keeganmoody33/YADIGGG/physical-design/logo-refinement-brief.md

---
title: "Logo Refinement Brief"
project: yadiggg
status: active-draft
type: brand_identity_brief
tags: [yadiggg, logo, brand-identity, visual-consistency]
backlinks:
  - "[[CONTEXT]]"
  - "[[docs/project-state]]"
  - "[[yadiggg_brand_identity_and_design_guidelines]]"
  - "[[physical-design/render-consistency-protocol]]"
---

# yadiggg Logo Refinement Brief

## Purpose

This brief defines the direction for refining the yadiggg logo so it supports the locked physical product direction instead of drifting into unrelated merch, packaging, or generic record-store iconography.

## Source Materials Reviewed

| Asset | Observed content | Role |
|---|---|---|
| `IMG_3581_converted.png` | Hand-drawn notebook sketch with rough black mark, red shovel/speaker head, green wave/energy strokes, handwritten `yadiggg.xyz` | Primary conceptual source |
| `yadigggsketch_rendered.png` | Cropped/cleaned version of the same sketch; large diagonal handle, red triangular/conical head, sweeping green/black wave marks | Primary conceptual source |
| `Ab0366a7e4d1c4f86ba5eb0a115a0dd80k.png` | Polished orange-on-black graphic with record circle, shovel/needle shape, and `yadiggg` wordmark | Reference-only / partially rejected |
| `yadiggg_brand_identity_and_design_guidelines.md` | Defines the intended metaphor: shovel digging downward, speaker cone in the shovel head, neon soundwave arcs, compact geometric wordmark | Active design requirement |

## Core Logo Metaphor

The refined logo should express:

> A shovel-speaker mark: a shovel digging into vinyl/ground, where the shovel head also reads as a red speaker cone and emits green sound/light-wave energy.

It should work at two distances:

1. **Small / far away**: reads as a shovel digging downward.
2. **Large / close up**: reveals the speaker-cone head and soundwave/energy arcs.

## What Must Be Preserved

- `yadiggg` as the wordmark, not `Crate IQ`.
- Shovel/digging metaphor.
- Audio/speaker metaphor.
- Vinyl/record/crate-digging culture.
- Raw underground energy, but cleaned into a usable hardware brand mark.
- Compatibility with the locked product CMF: smoke-clear shell, dark internals, amber/orange control, monochrome display.

## What Must Change

- The rough sketch must become a scalable vector-like mark.
- The shovel must not read as a generic spade or random microphone stand.
- The polished orange logo should not remain the final direction because it loses the red speaker cone and neon wave energy from the sketch.
- The logo should not be merch-first or oversized on the hardware.
- The wordmark should be cleaner and more controlled than the handwritten `.xyz` sketch.

## Color Direction

| Role | Color | Notes |
|---|---|---|
| Primary dark | Obsidian Charcoal `#1A1A1D` | Main background / hardware-system anchor |
| Hardware accent | Amber Orange `#E07A5F` | Scan-button and warm brand accent |
| Speaker focal point | Speaker Red `#D83232` | Use sparingly inside the shovel/speaker head |
| Energy accent | Neon Wave Green `#72FF66` | Sound/light arcs only; not the whole logo |
| Neutral | Cream White `#F4F1DE` | Alternate contrast color for screen/etch applications |

## Three Refinement Routes

### Route 1: Hardware Badge Mark

A compact geometric emblem designed for small etched or printed use on the device, packaging, and startup screen. Minimal details, strong silhouette, shovel head simplified into a speaker cone, 2–3 energy arcs.

Best for: immediate hardware consistency.

### Route 2: Underground Signal Mark

A more expressive mark that preserves more of the original sketch energy: diagonal shovel, red speaker cone, green sonic arcs, rough-but-controlled line rhythm.

Best for: brand personality, stickers, web, launch visuals.

### Route 3: Technical Wordmark Lockup

A clean `yadiggg` wordmark paired with a reduced shovel-speaker icon. More geometric, less illustrative, better for tiny screen, documentation, and engraved applications.

Best for: production identity system and small-scale legibility.

## Acceptance Criteria

A refined logo passes only if:

- It is original and does not resemble an existing brand logo.
- It reads as `yadiggg` when text is included.
- It avoids `Crate IQ` completely.
- It does not become a generic spade/turntable icon.
- The shovel and speaker idea are both legible.
- The mark still works in one-color form.
- The full-color form preserves red speaker focal point and green wave energy.
- It can scale down for hardware use without becoming visual noise.
- It does not conflict with the compact smoke-clear product direction.

## Prompt Direction

Use the hand sketch as conceptual source, not as a literal trace. Use the existing polished orange logo only as a warning/reference for what became too generic.

New logo explorations should be original, commercially safe, vector-like, and suitable for later manual refinement in SVG/vector tools.
