keeganmoody33/YADIGGG/Crate Iq Firmware Architecture.pdf

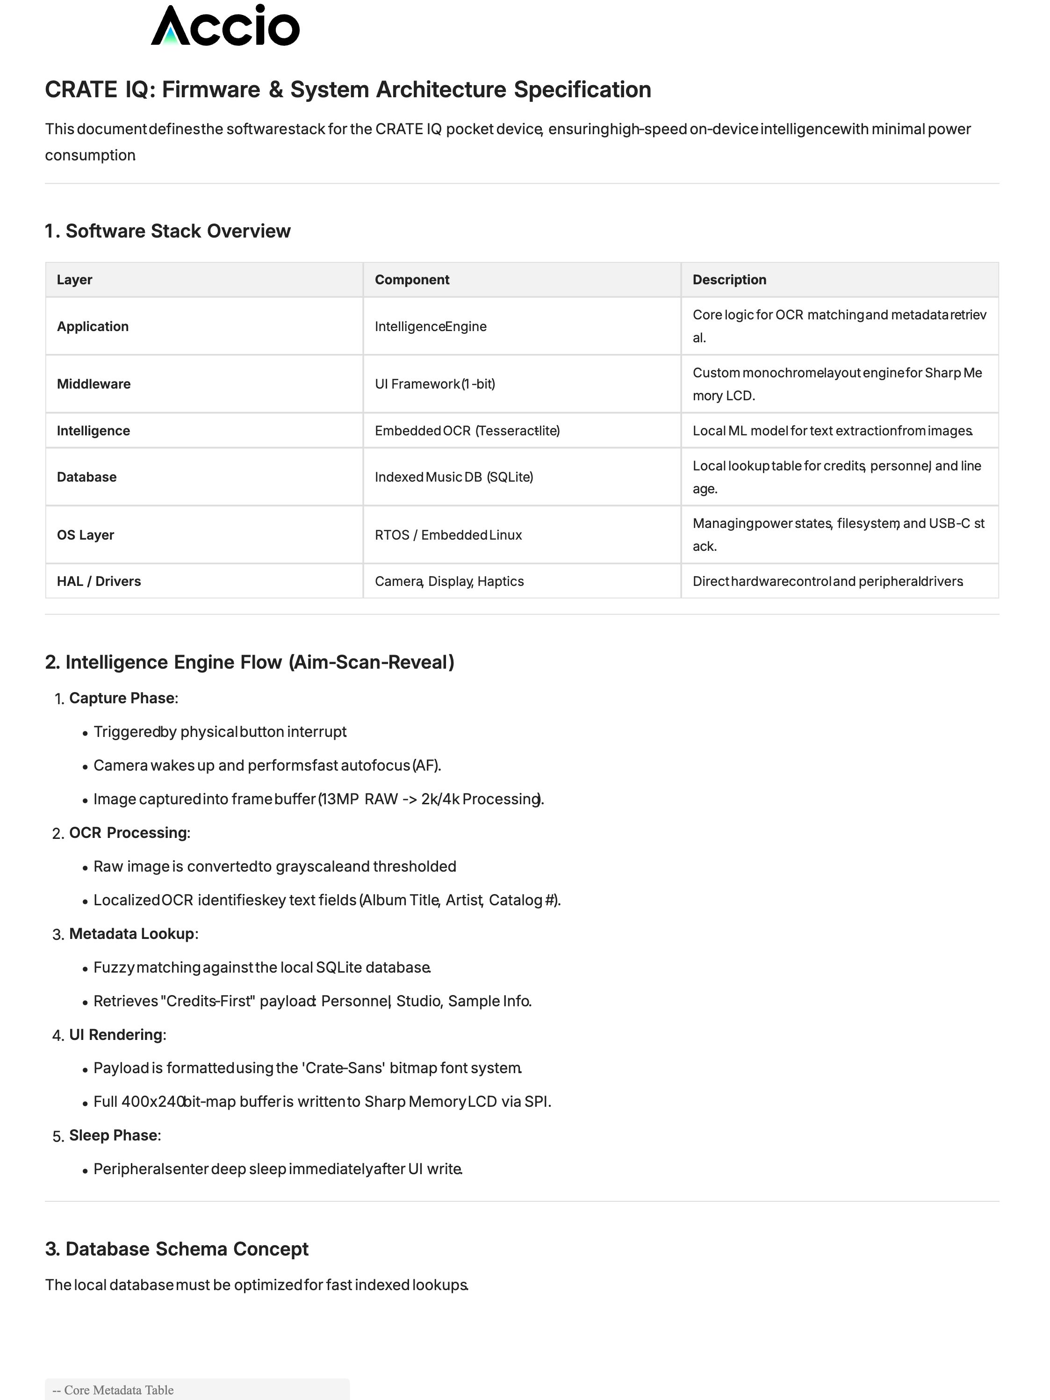
[picture p9: page 1]
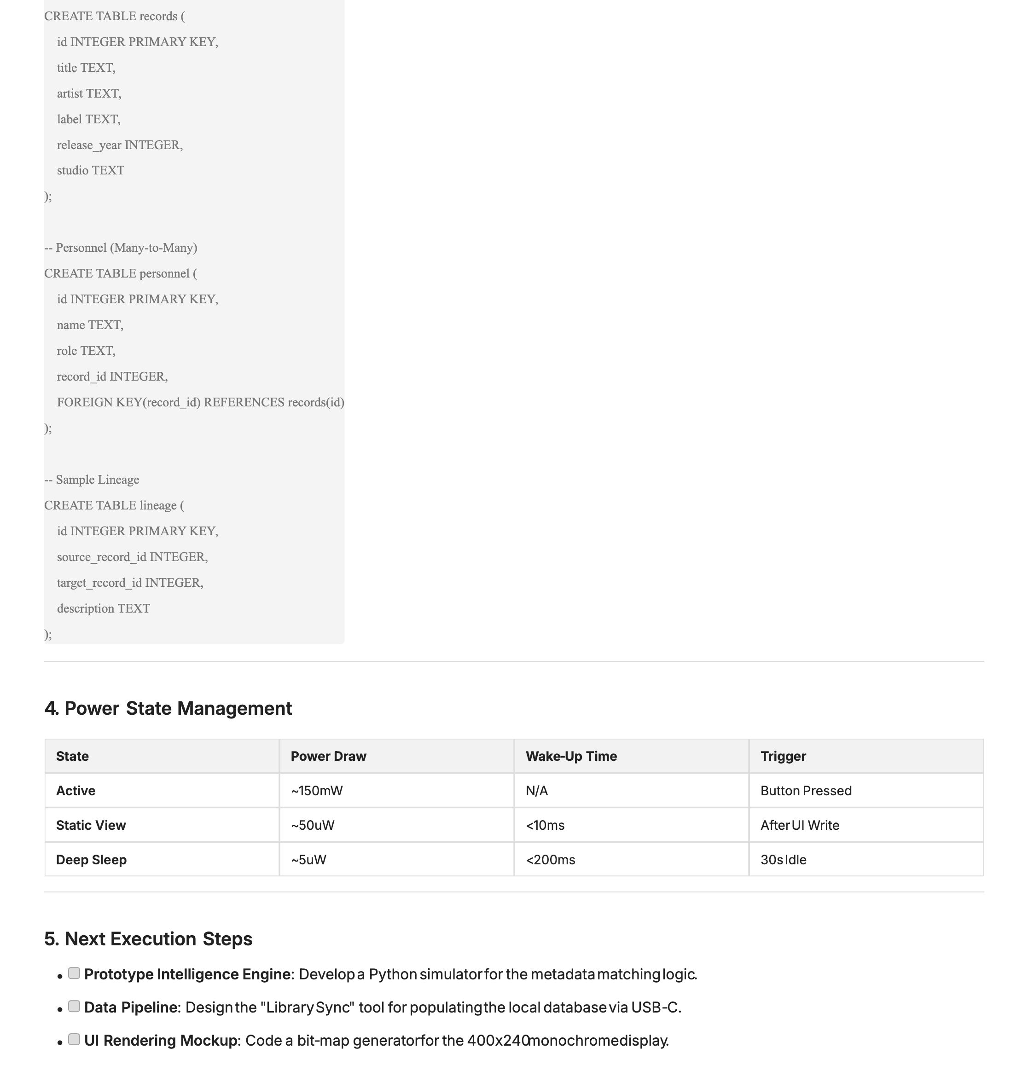
[picture p10: page 2]
