keeganmoody33/YADIGGG/Crate Iq Physical Specs.pdf

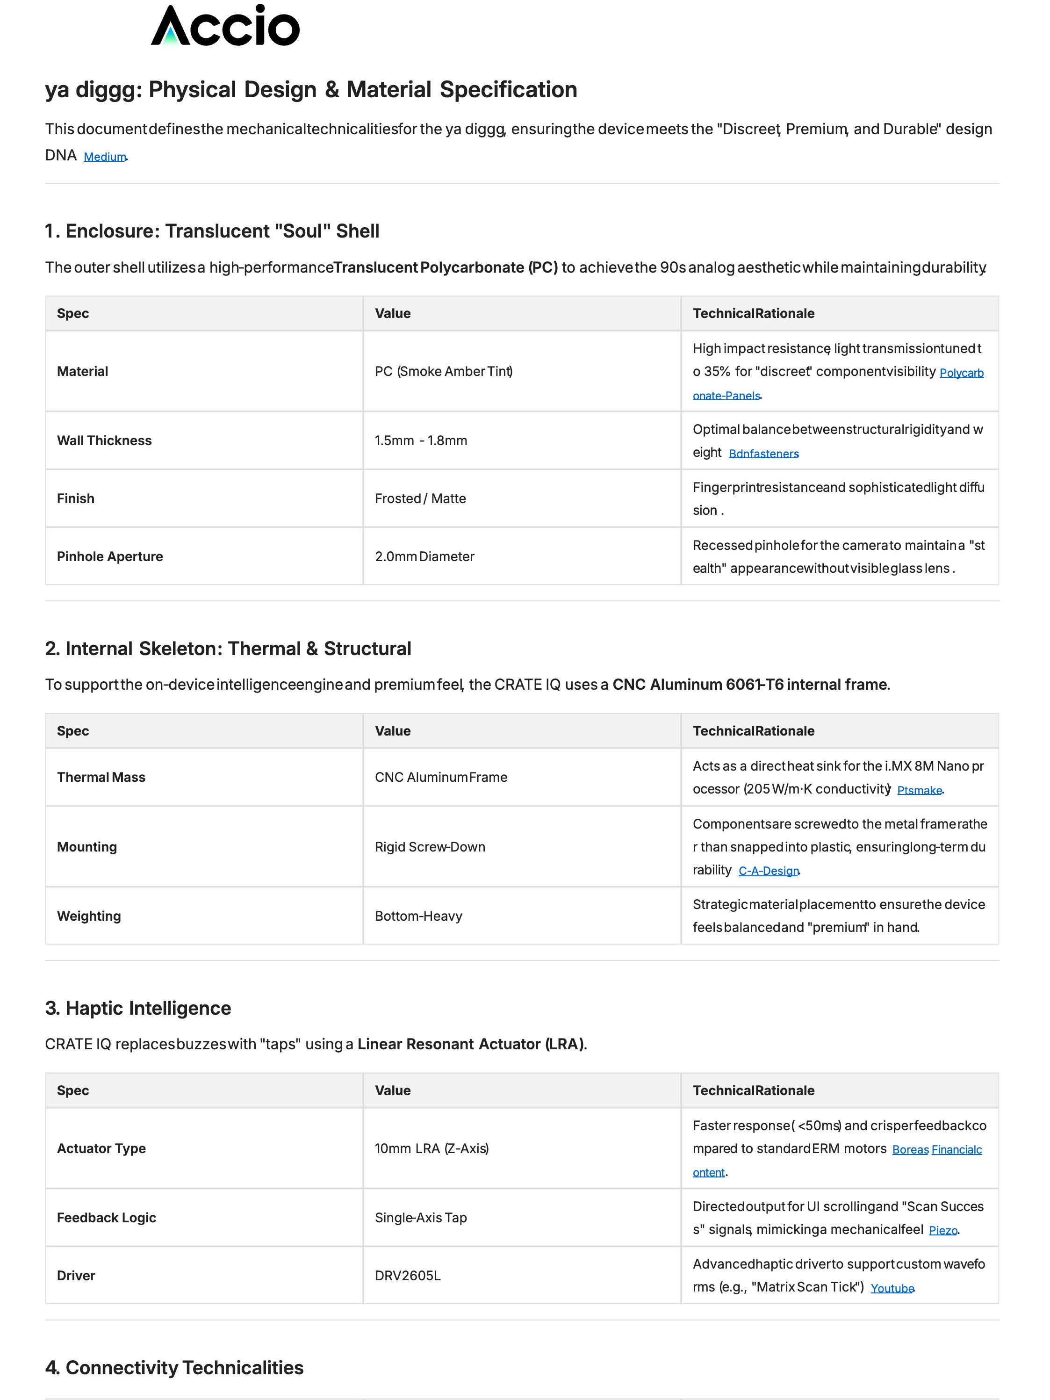
[picture p11: page 1]

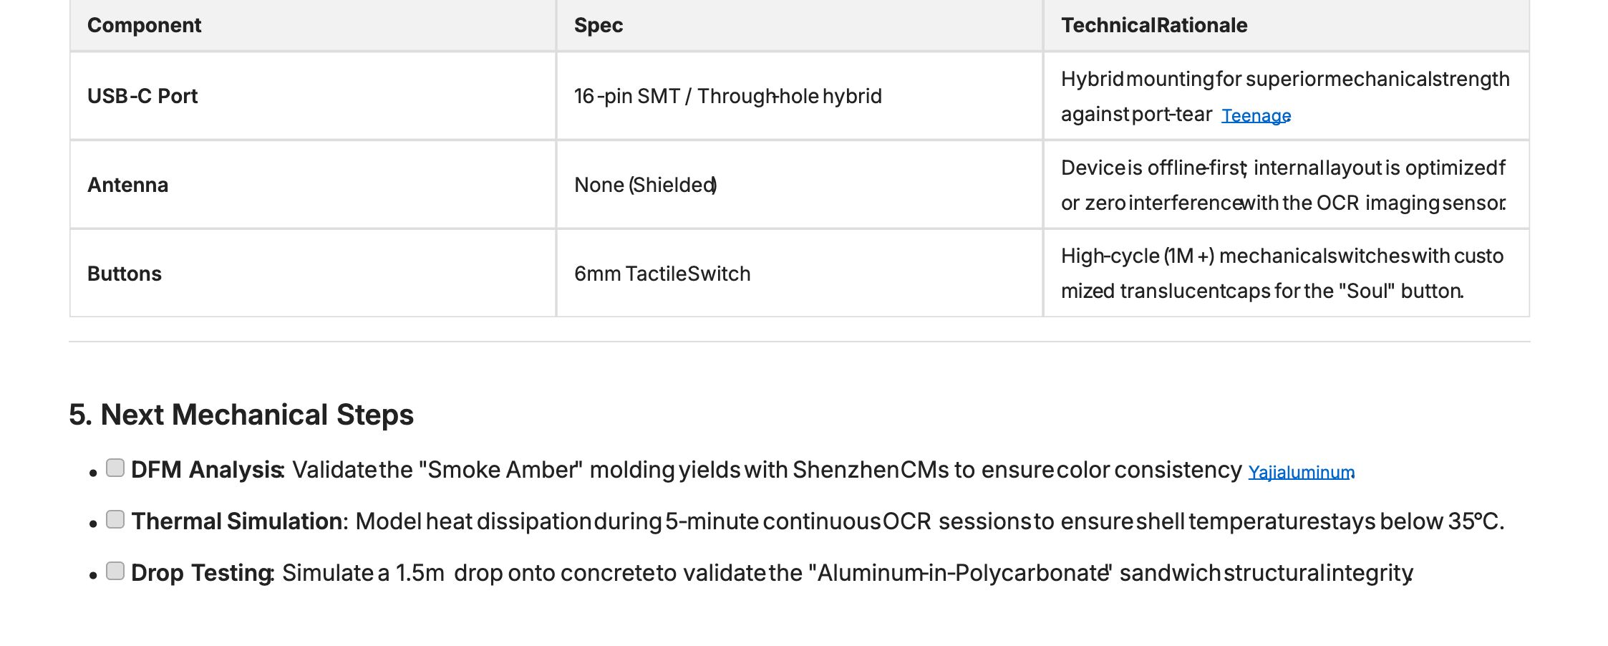
[picture p12: figure]
