keeganmoody33/YADIGGG/Ya Diggg Advanced Specs.pdf

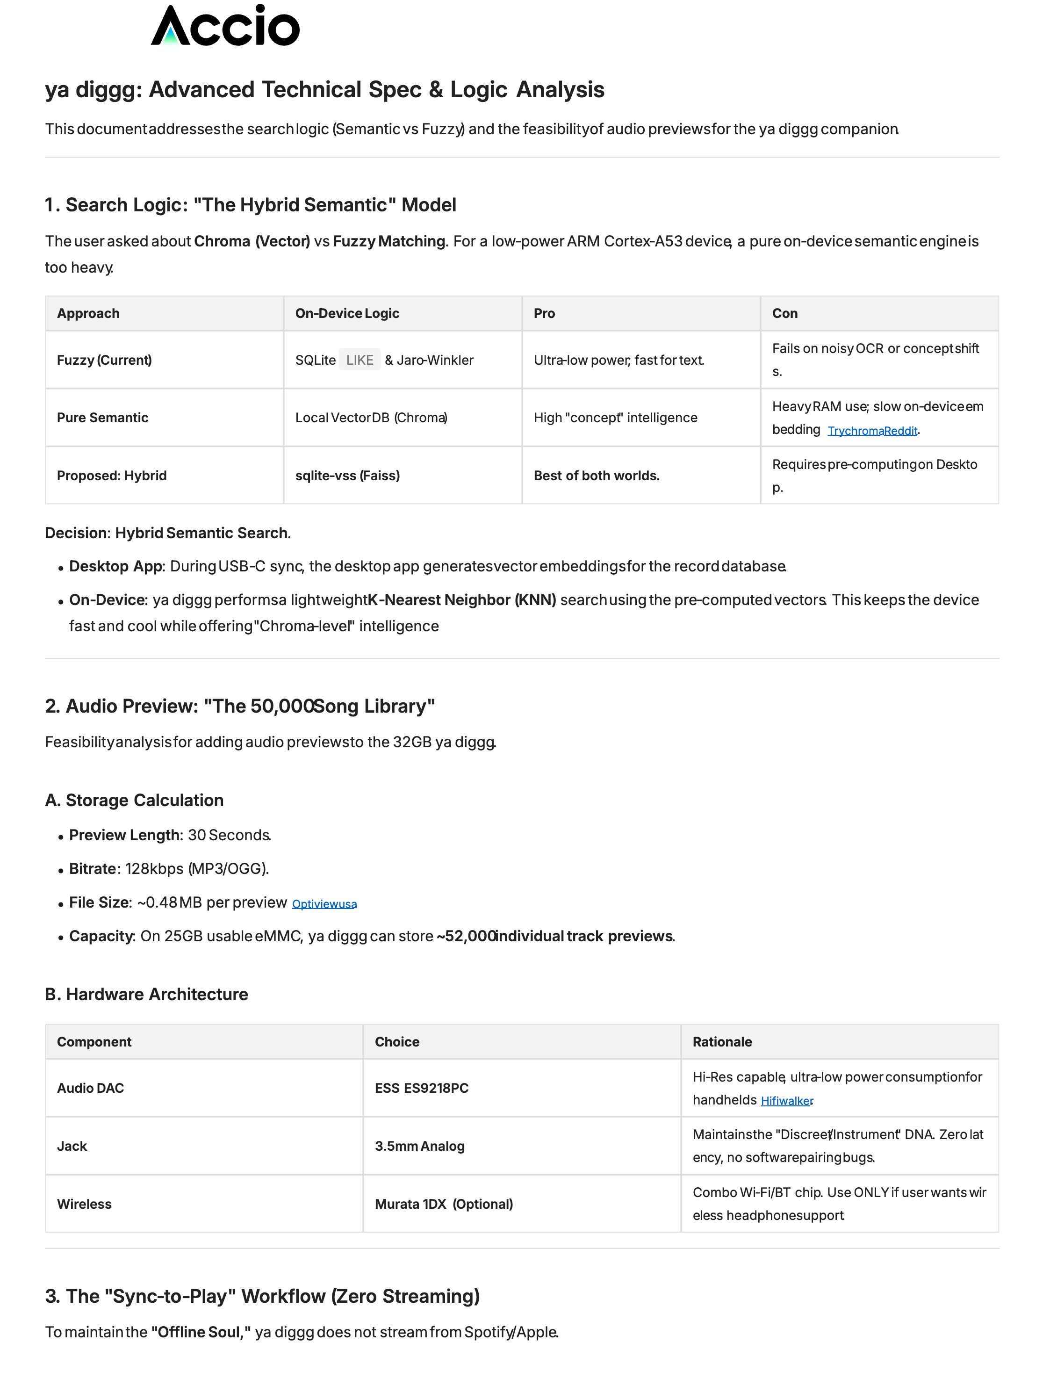
[picture p13: page 1]

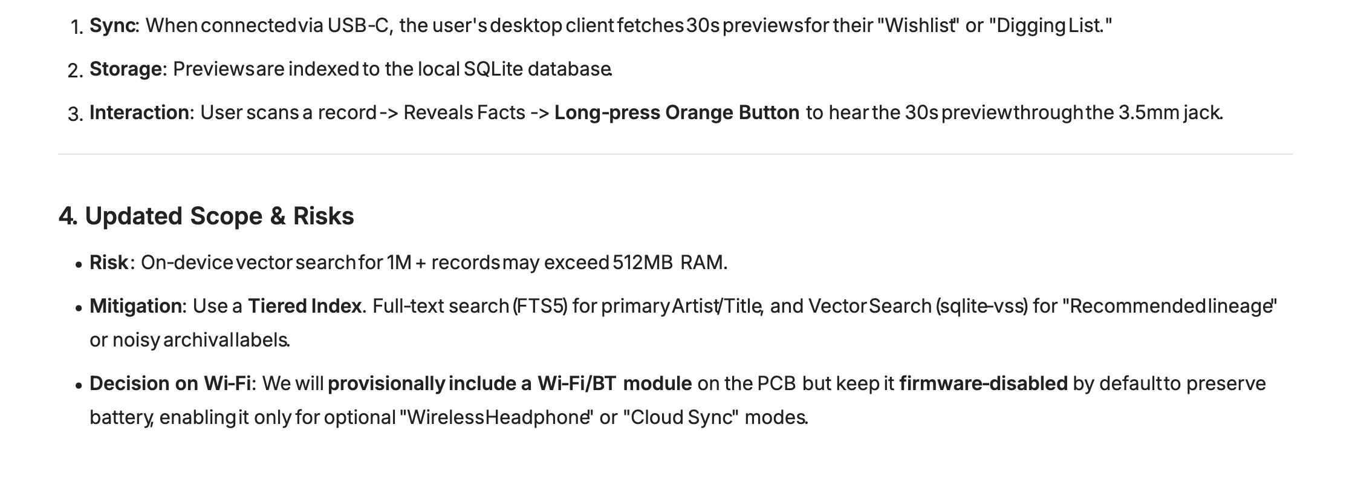
[picture p14: figure]
