keeganmoody33/YADIGGG/Ya Diggg Sonic Id Spec.pdf

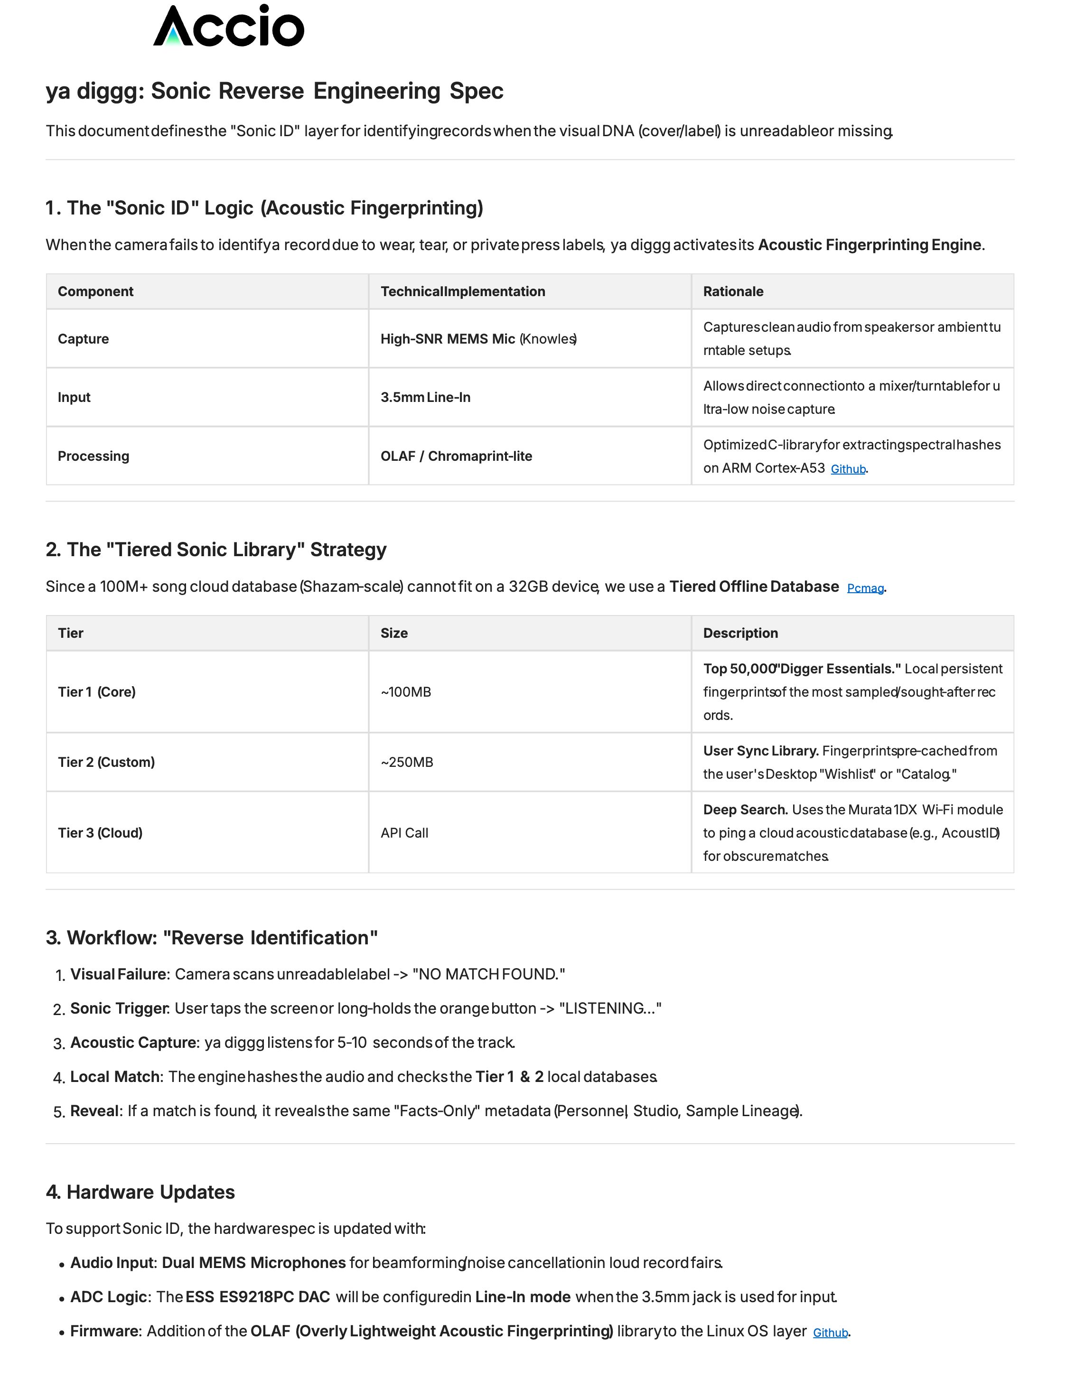
[picture p15: page 1]
