keeganmoody33/YADIGGG/Crate Iq Master Roadmap.pdf

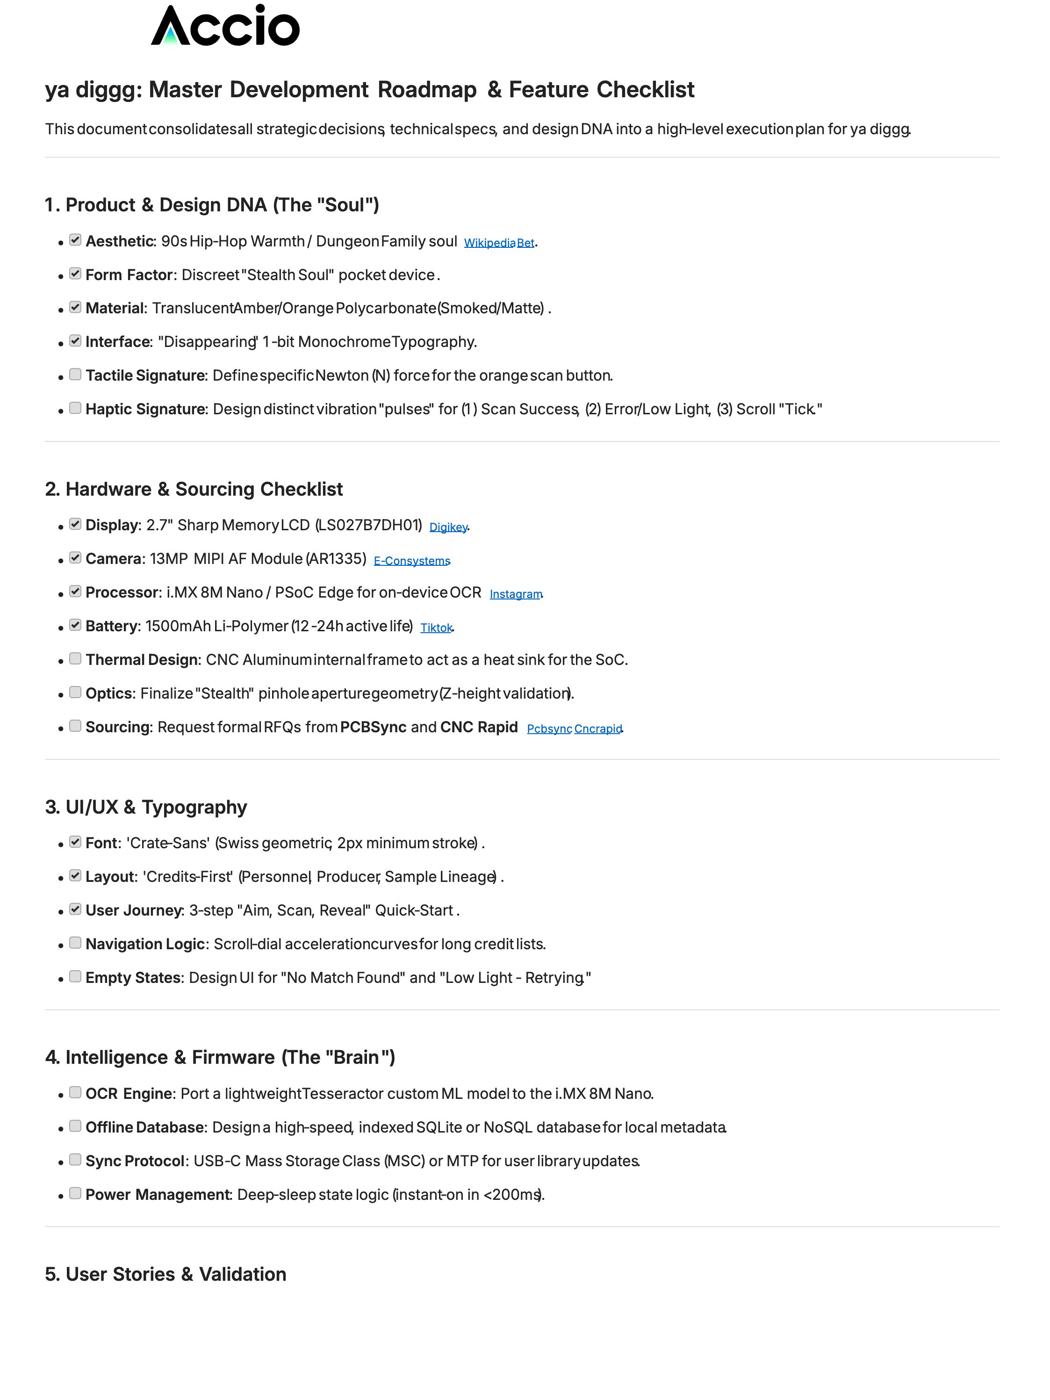
[picture p16: page 1]

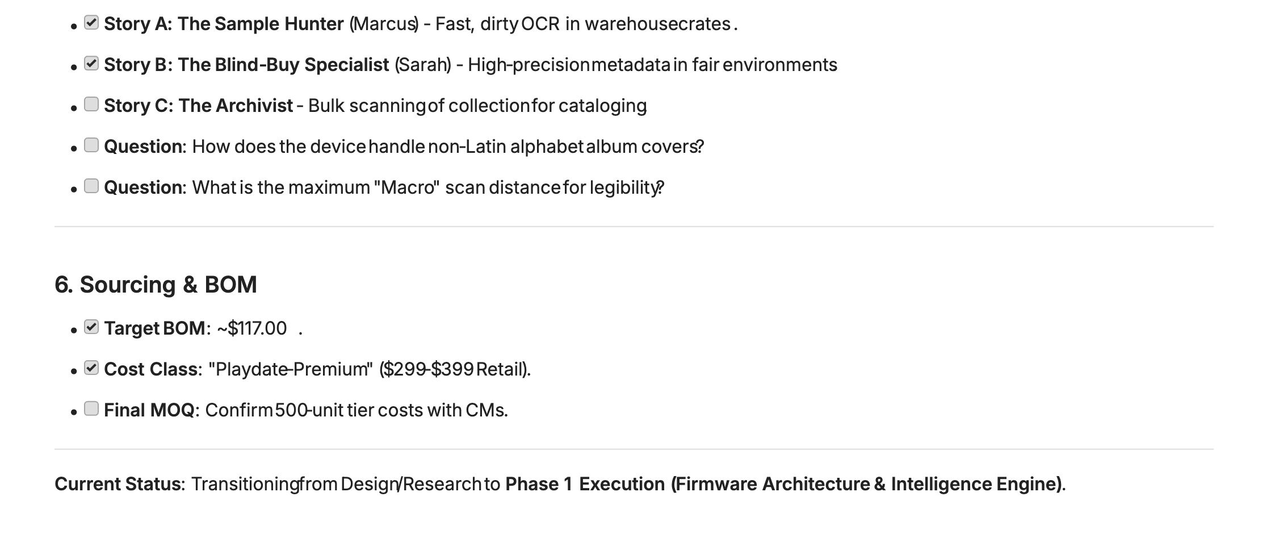
[picture p17: figure]
