keeganmoody33/YADIGGG/Crate Iq Quick Start.pdf

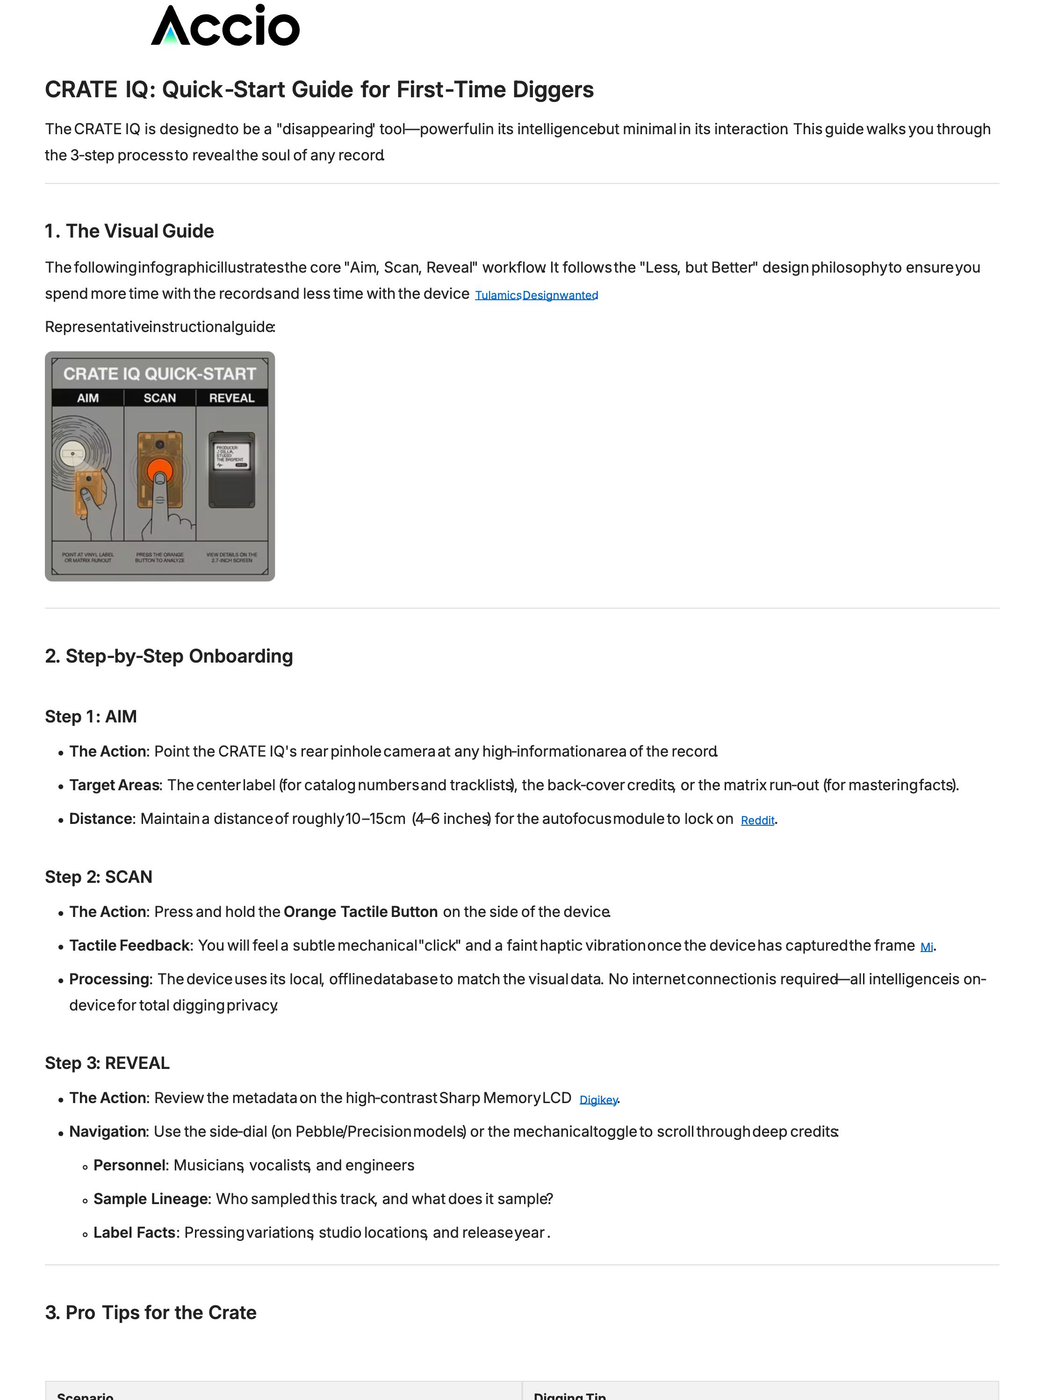
[picture p18: page 1]

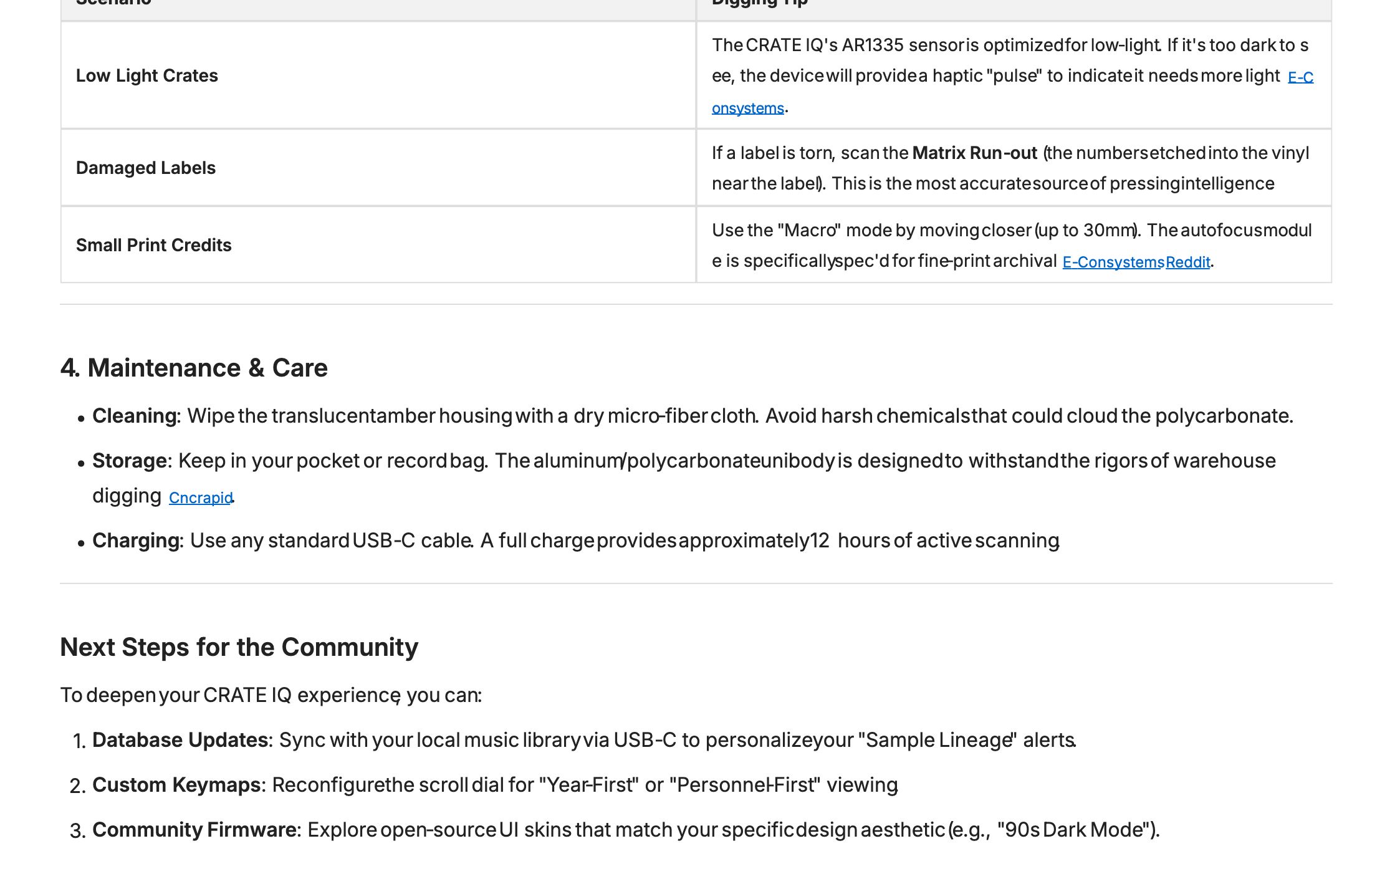
[picture p19: figure]
