keeganmoody33/YADIGGG/Crate Iq Scope Document.pdf

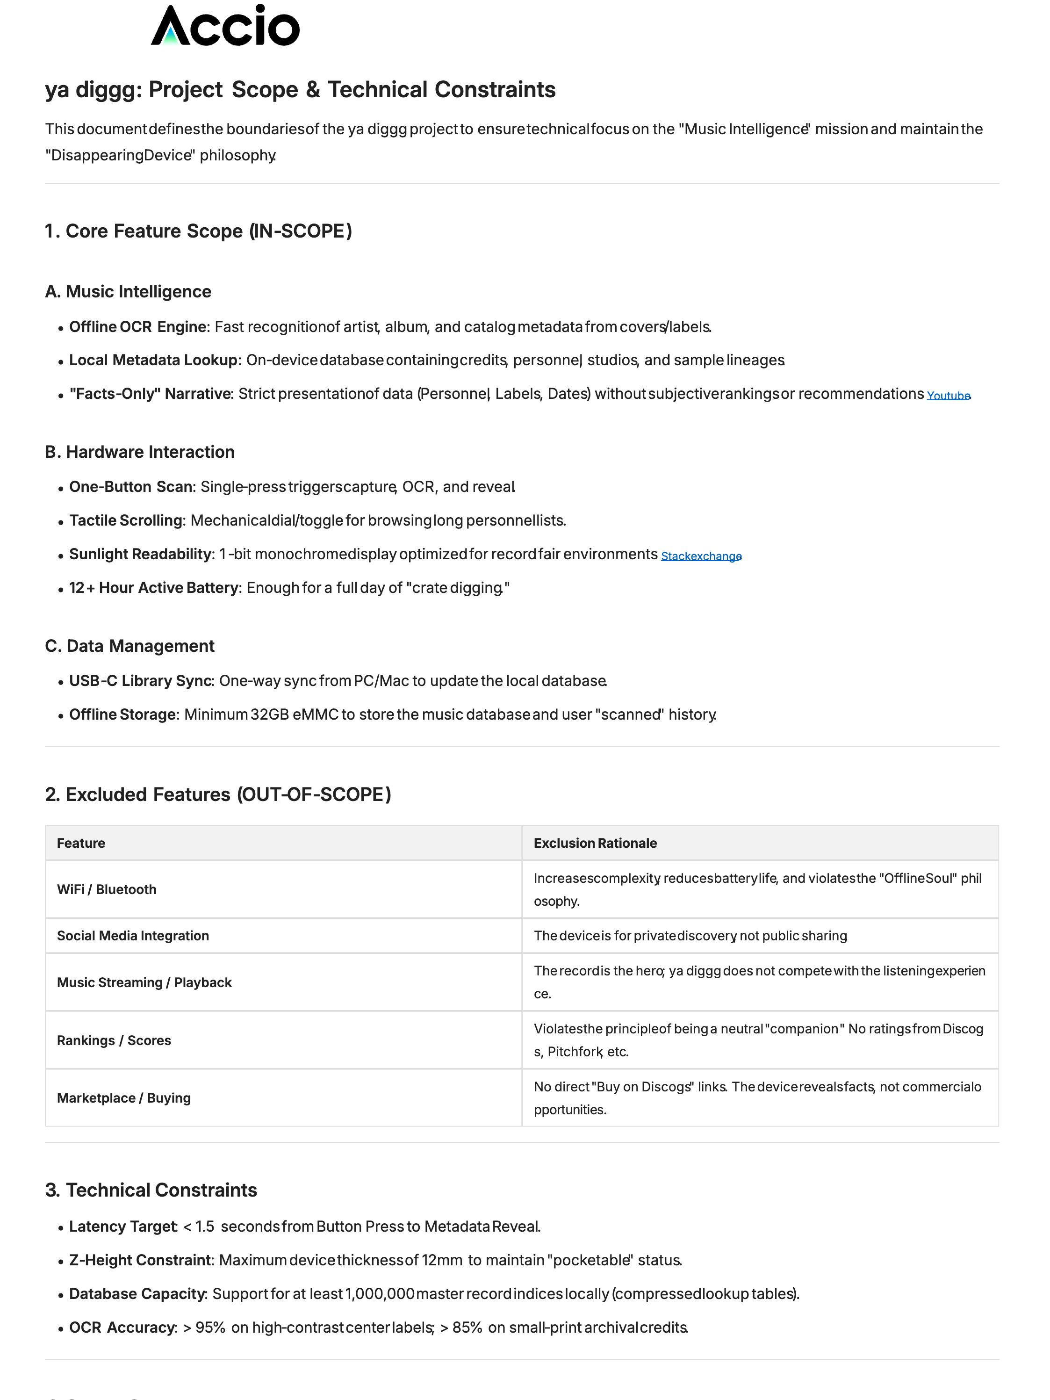
[picture p20: page 1]
