keeganmoody33/YADIGGG/Crate Iq User Interactions.pdf

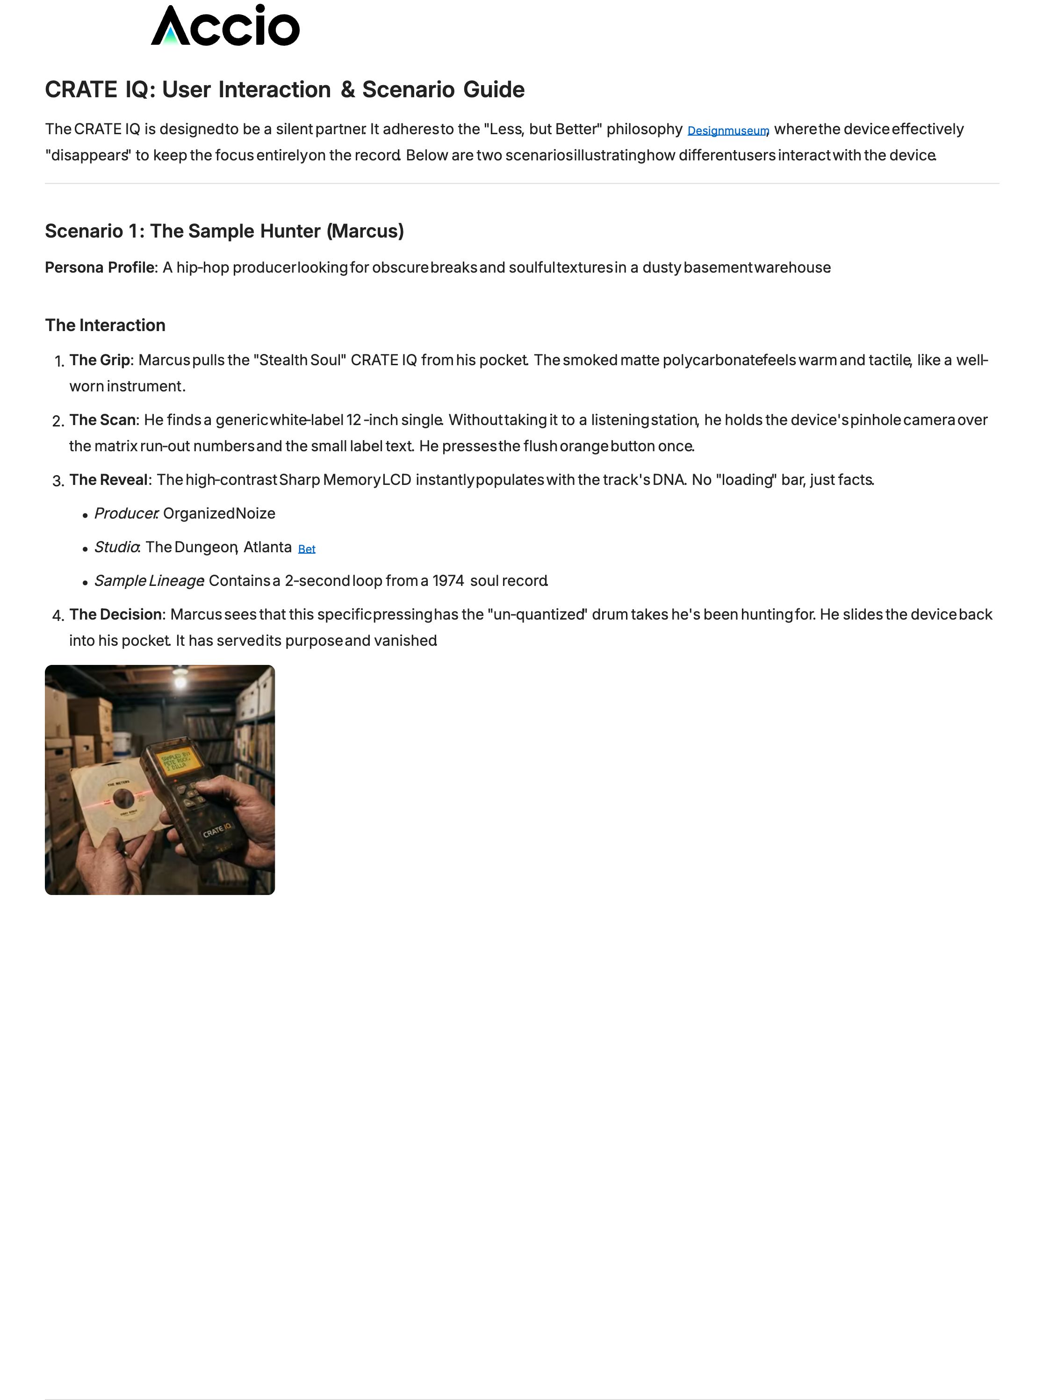
[picture p21: page 1]
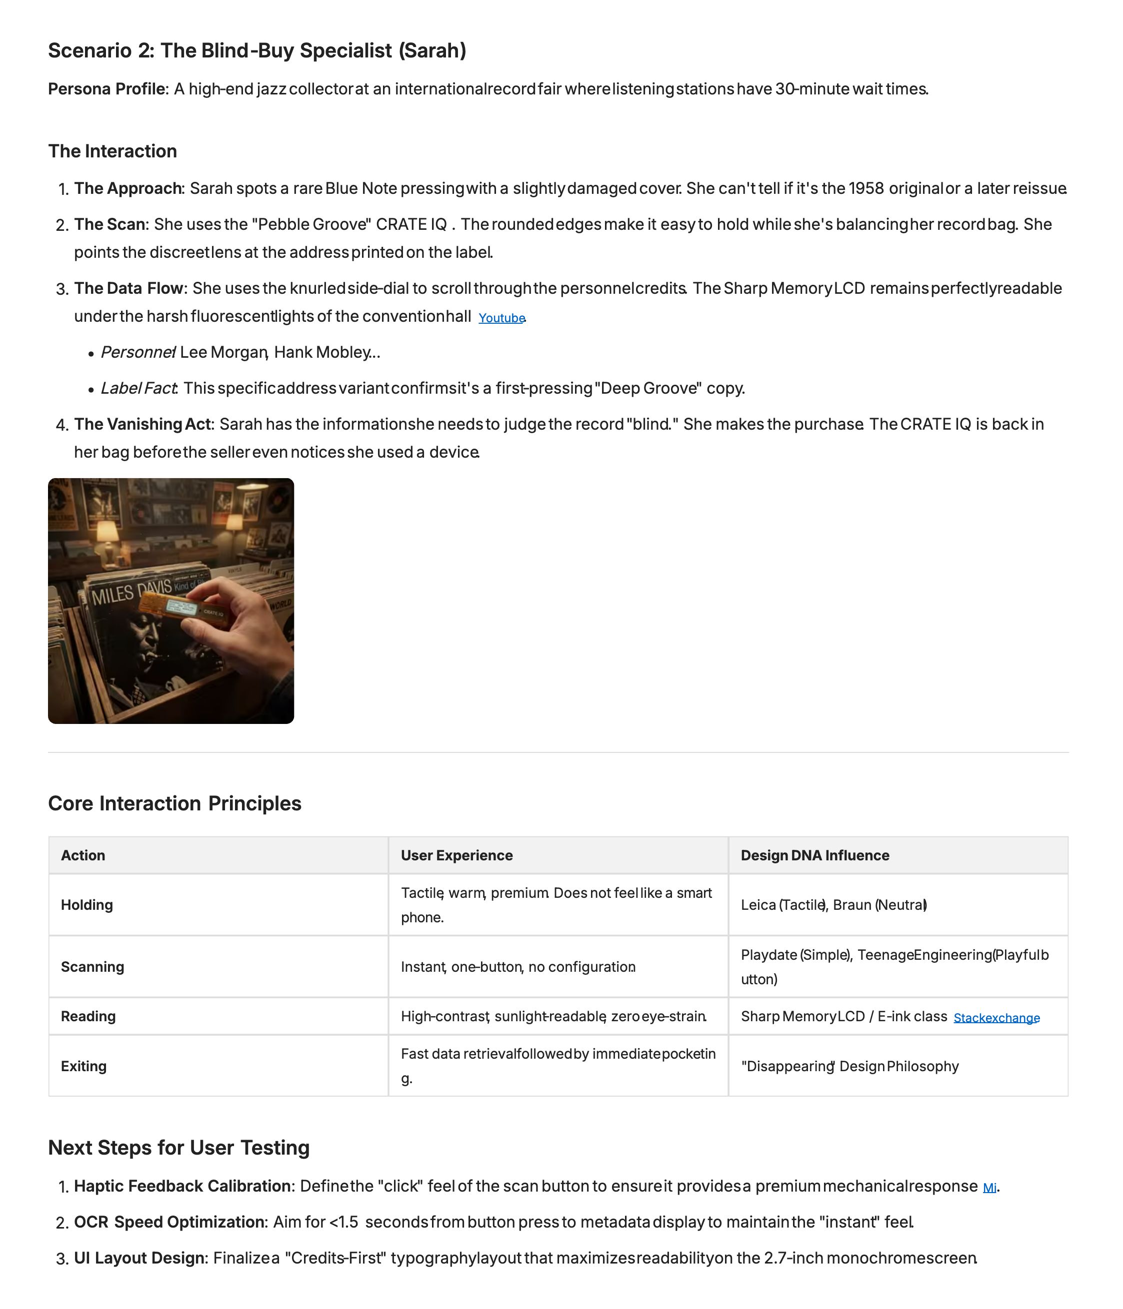
[picture p22: page 2]
