keeganmoody33/YADIGGG/Ya Diggg Official Tech Pack.pdf

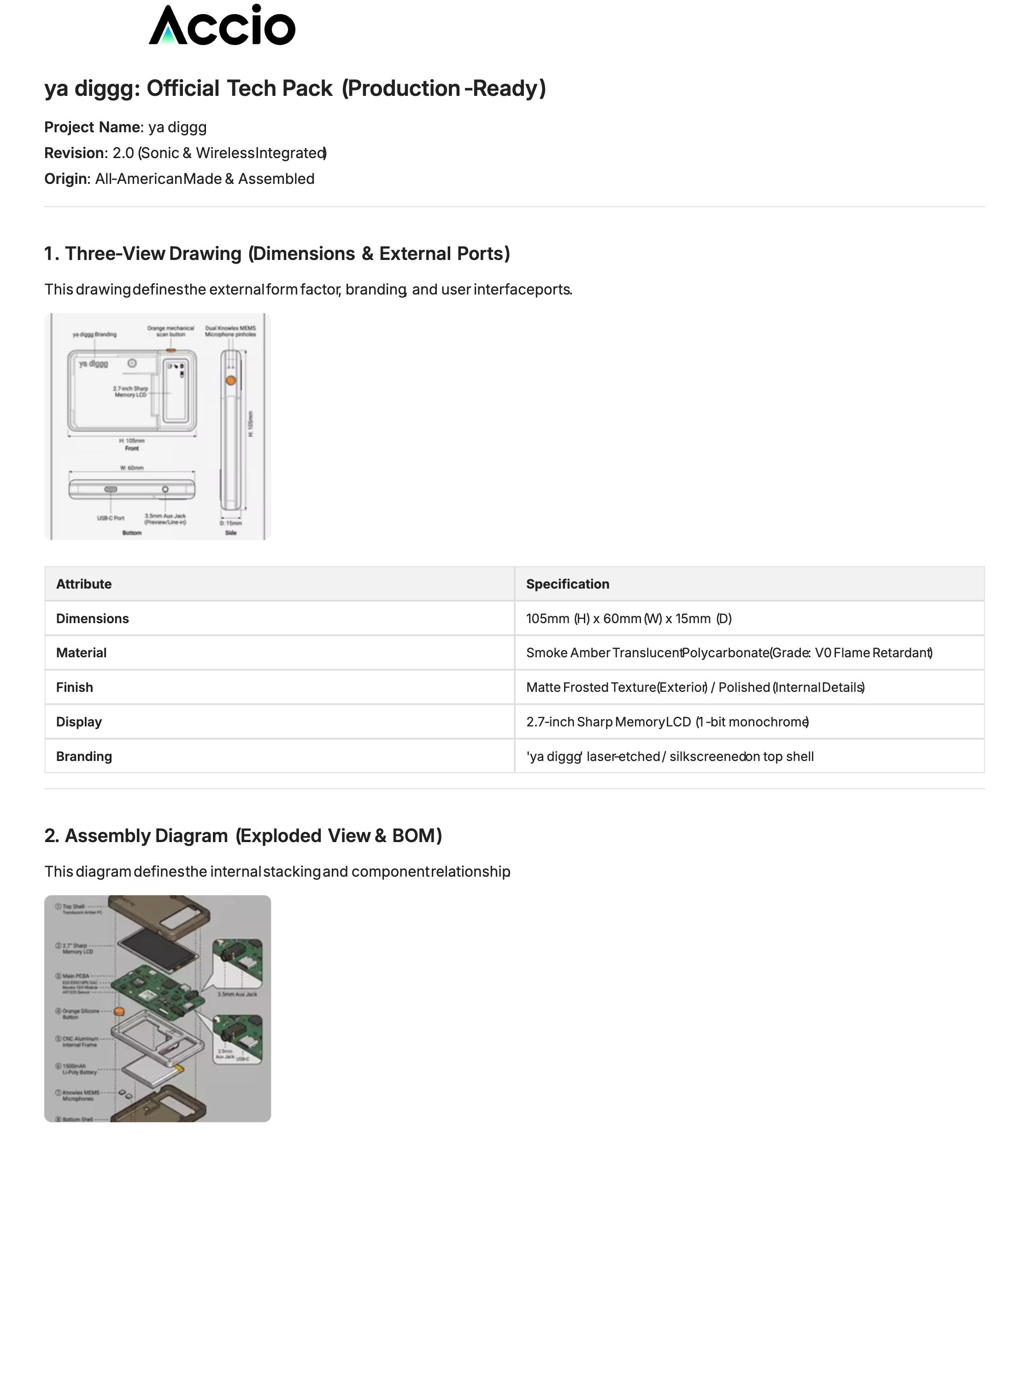
[picture p23: page 1]
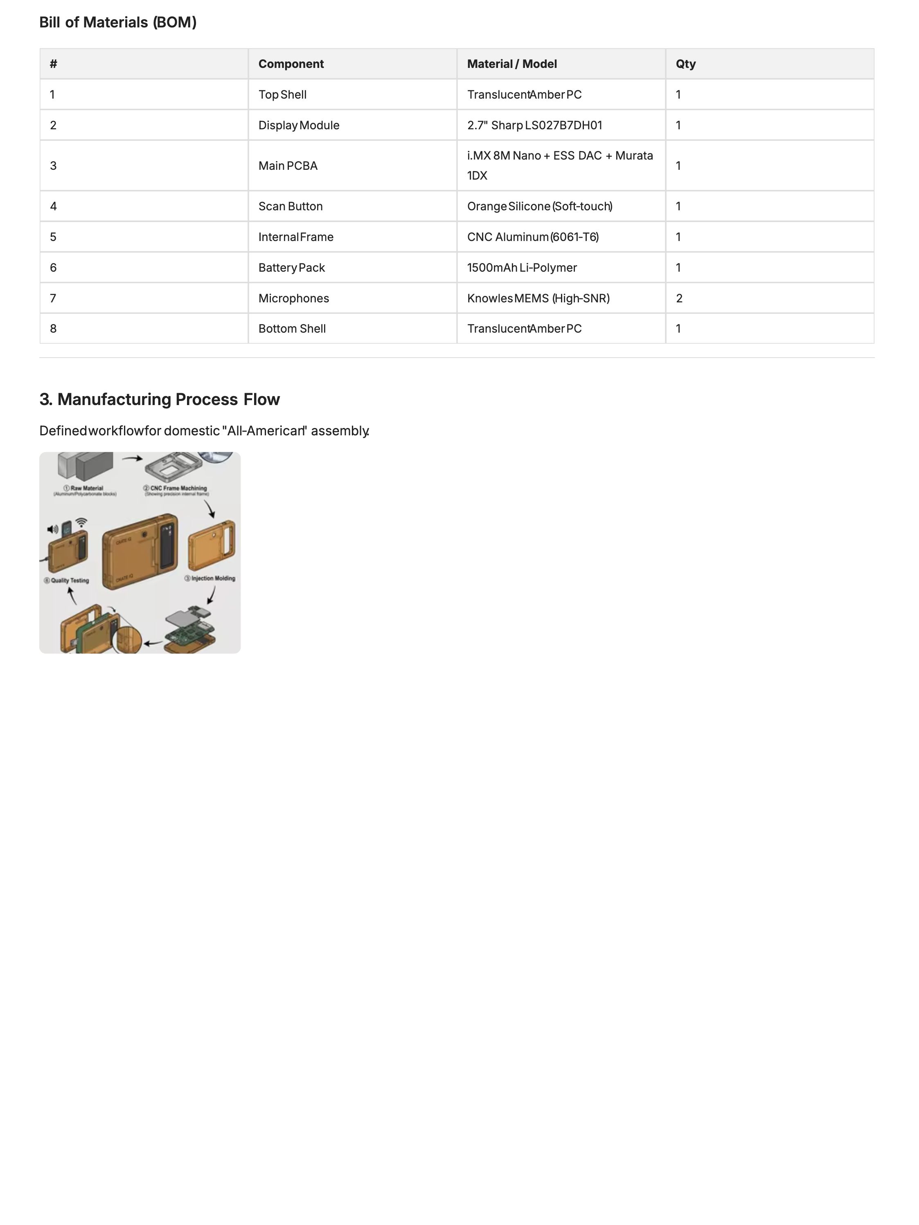
[picture p24: page 2]

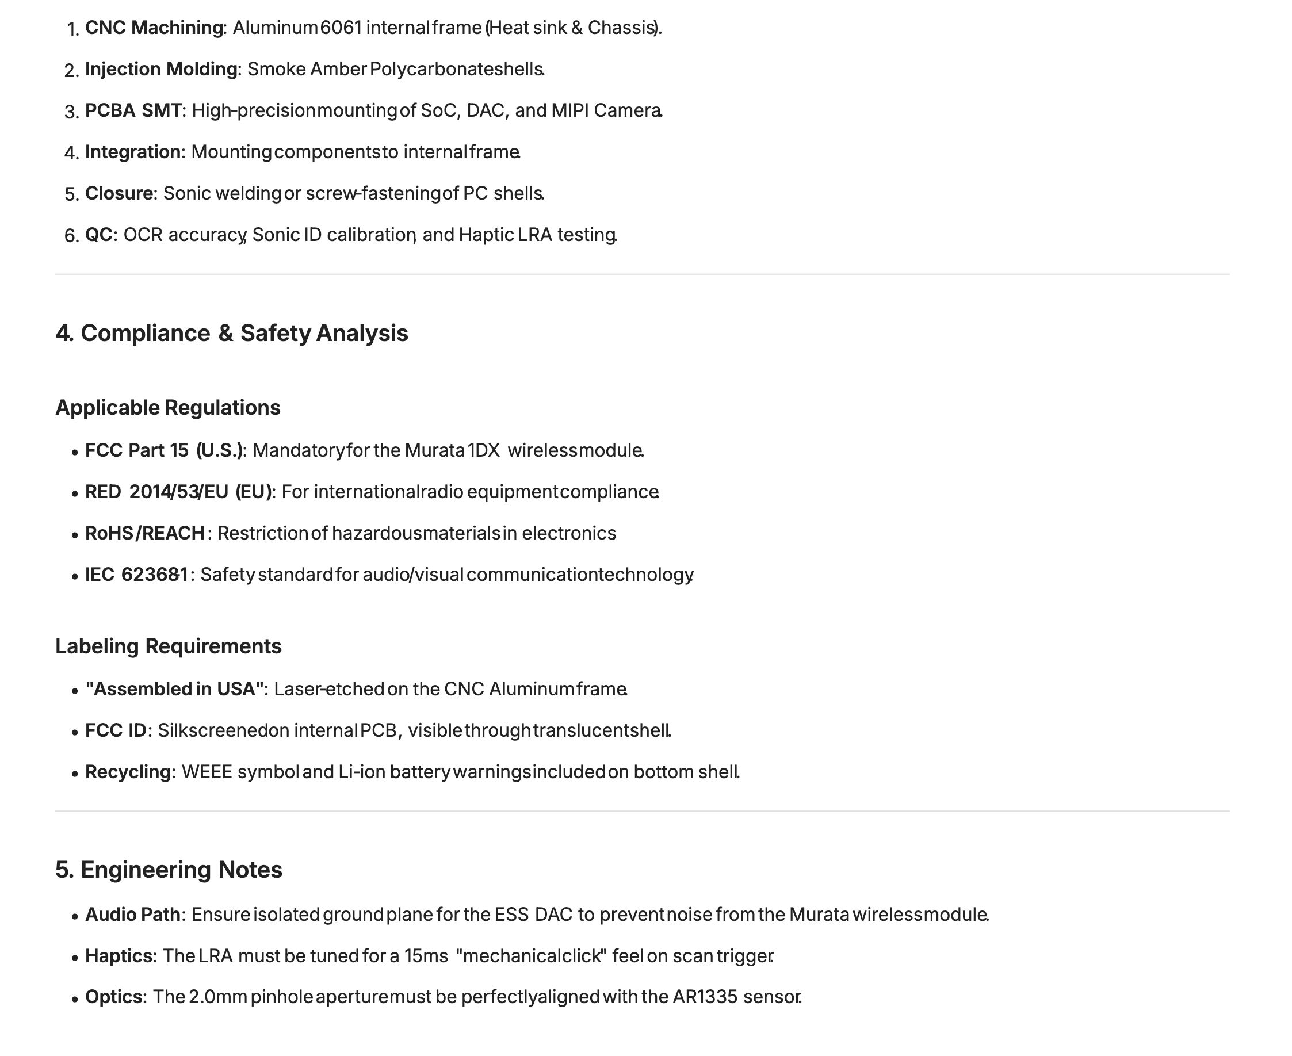
[picture p25: figure]
