keeganmoody33/YADIGGG/Crate Iq Scope Document.pdf.png

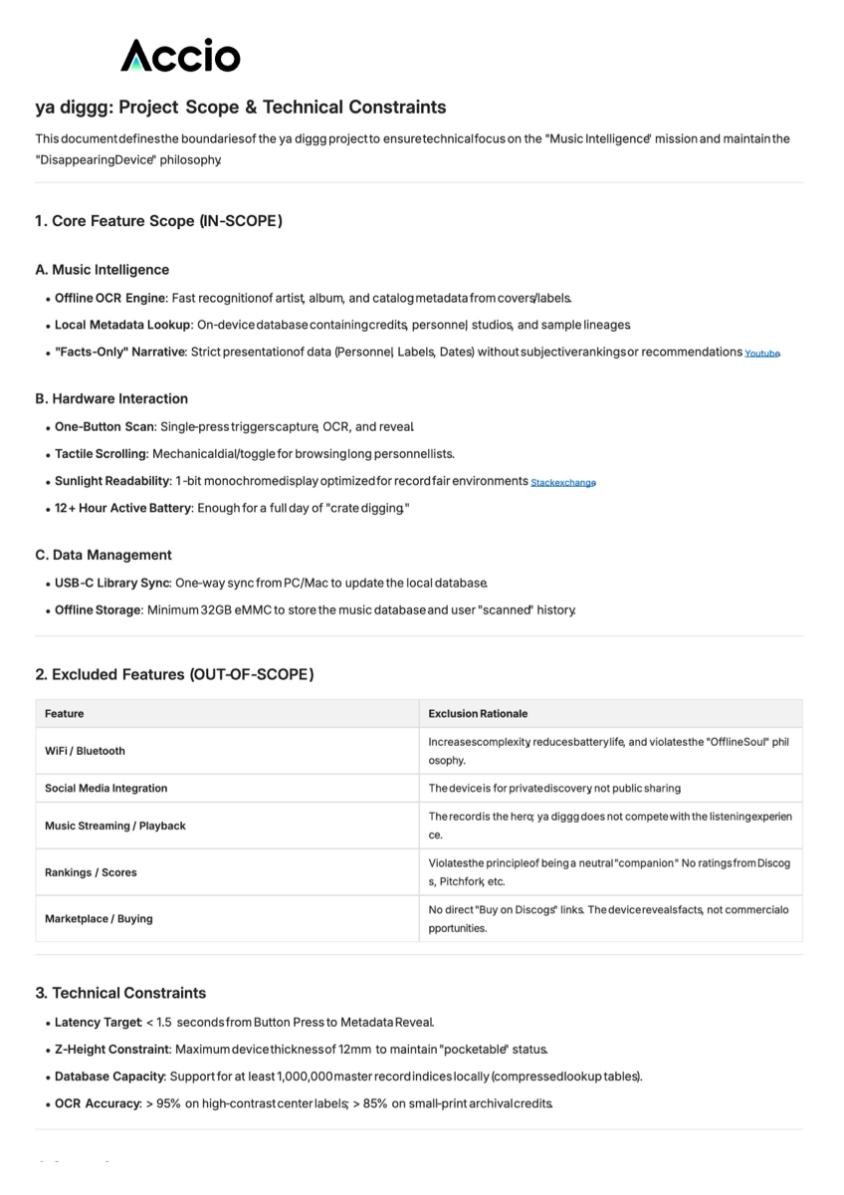
Crate Iq Scope Document.pdf.png
