keeganmoody33/YADIGGG/IMG_3581_converted.png

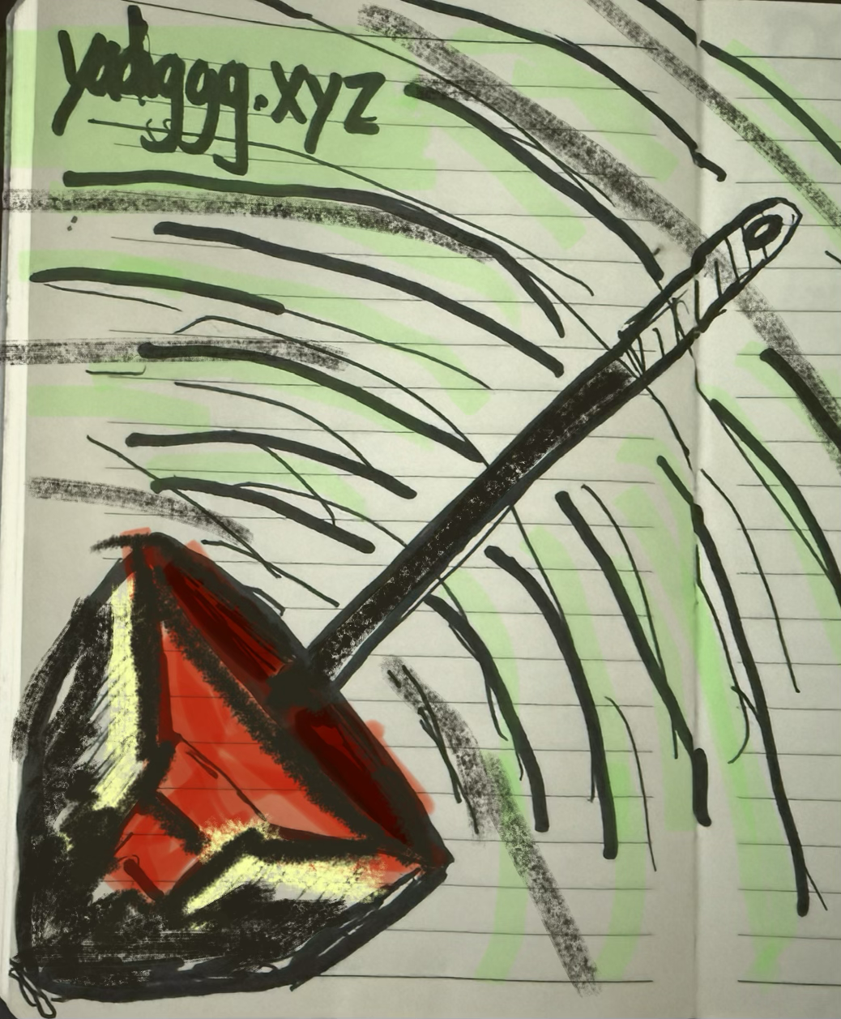
IMG_3581_converted.png
