keeganmoody33/YADIGGG/media-output/img-mujspg9r-88019fbf.png

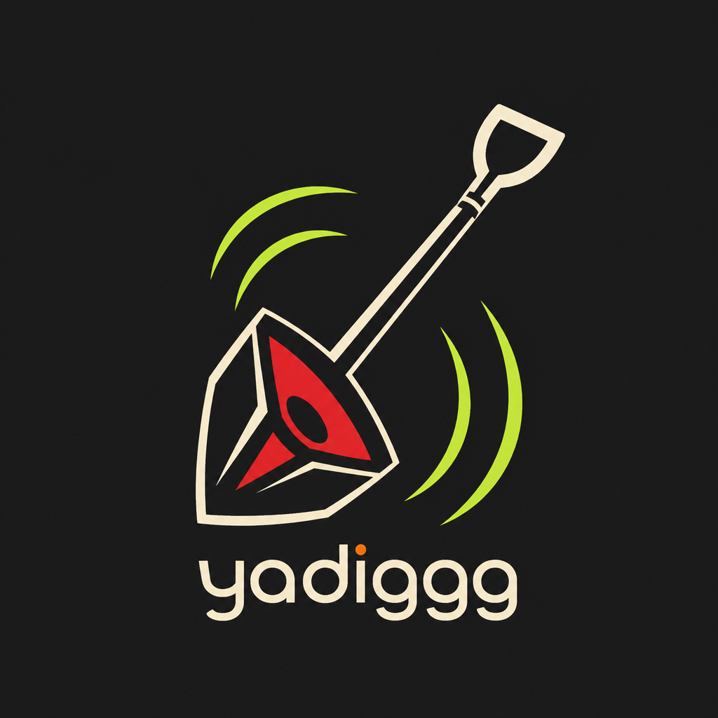
media-output/img-mujspg9r-88019fbf.png
