keeganmoody33/YADIGGG/media-output/img-mujspgo1-16f6e9df.png

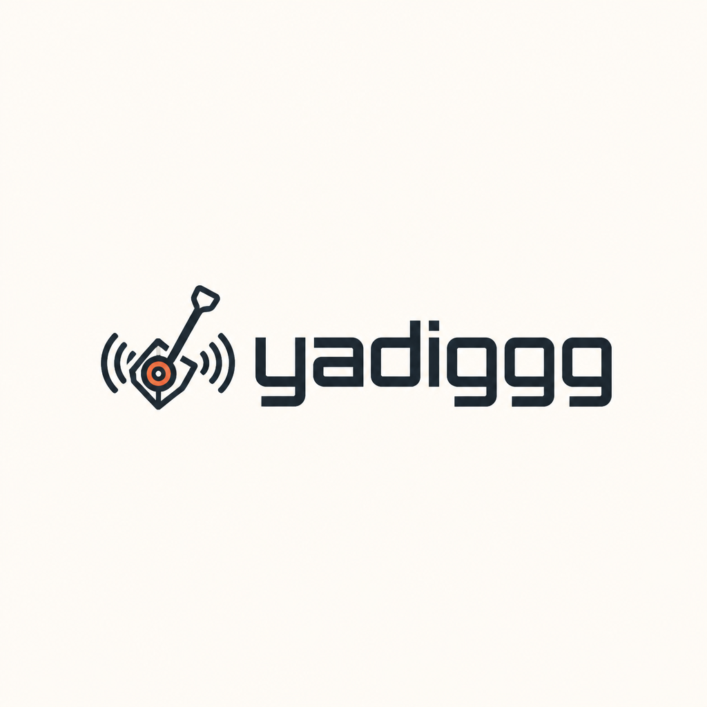
media-output/img-mujspgo1-16f6e9df.png
