keeganmoody33/YADIGGG/media-output/img-mujspi8y-83e51195.png

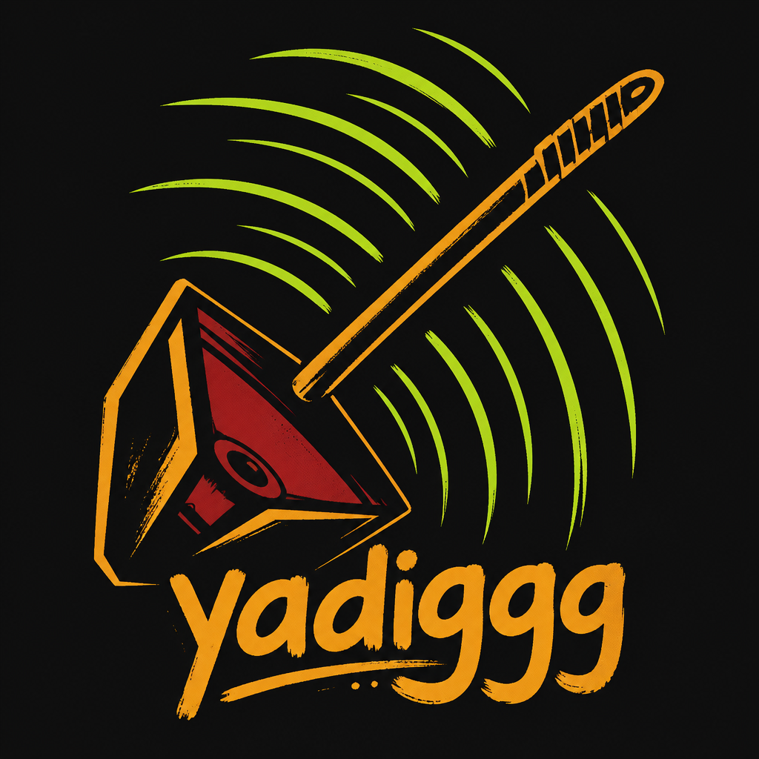
media-output/img-mujspi8y-83e51195.png
