keeganmoody33/YADIGGG/rendered_pages/Crate Iq Firmware Architecture_p2.png

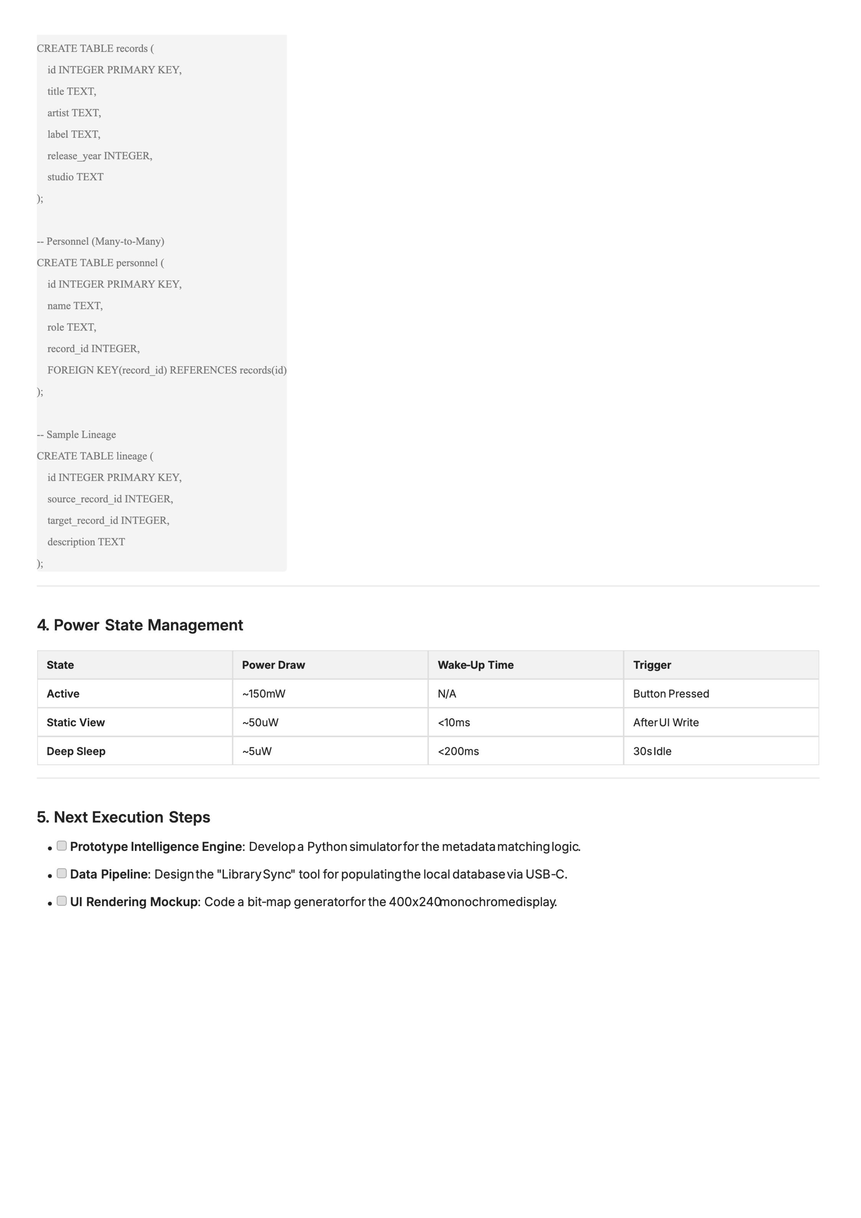
rendered_pages/Crate Iq Firmware Architecture_p2.png
