keeganmoody33/YADIGGG/rendered_pages/Crate Iq Master Roadmap_p1.png

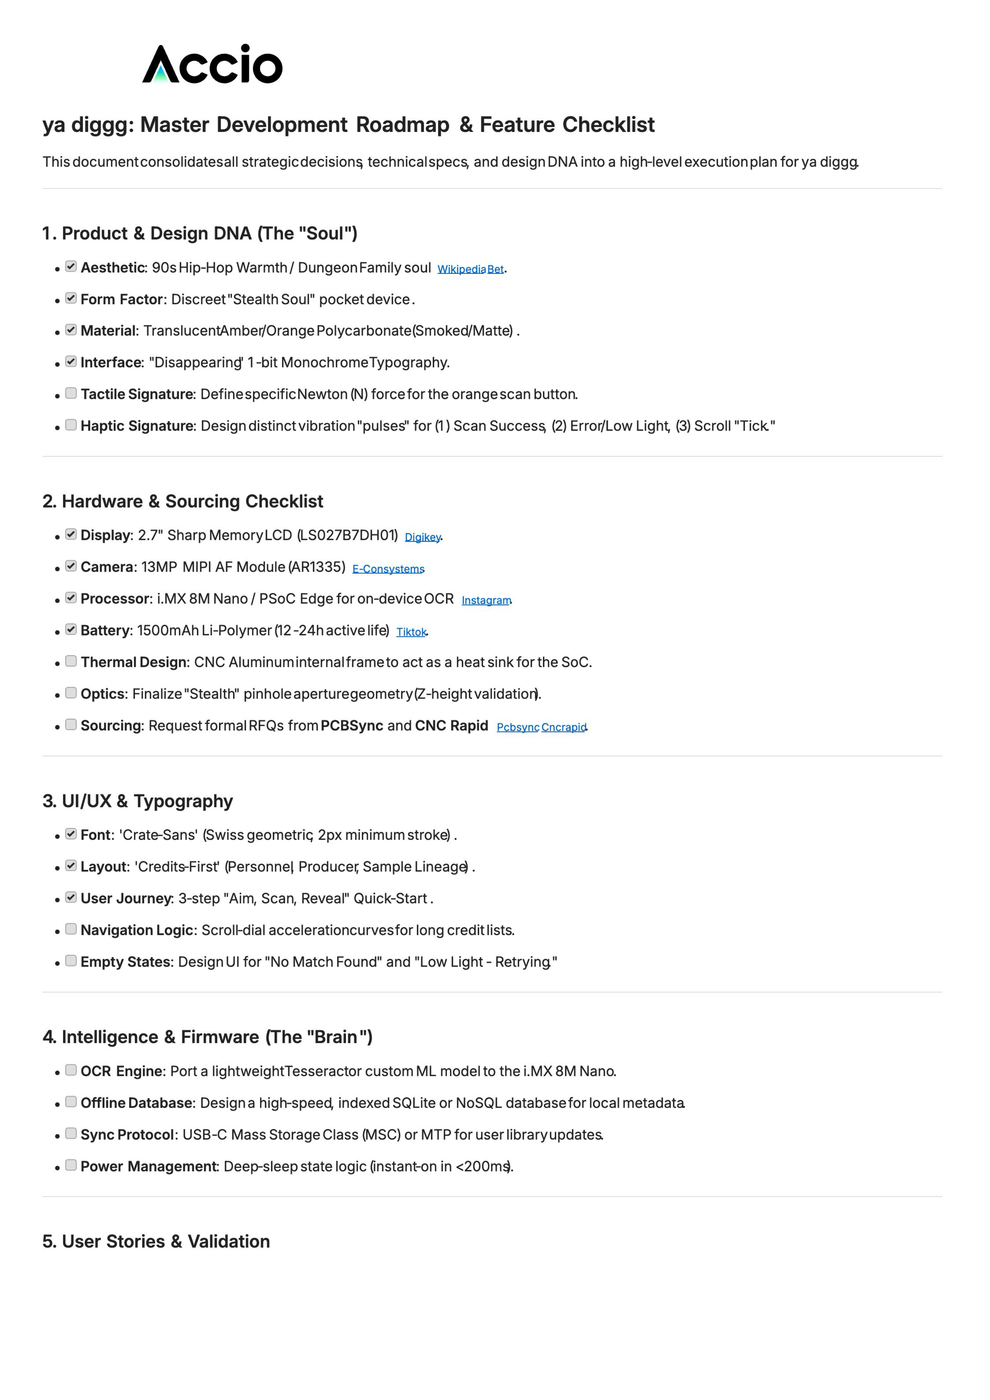
rendered_pages/Crate Iq Master Roadmap_p1.png
