keeganmoody33/YADIGGG/rendered_pages/Crate Iq Master Roadmap_p2.png

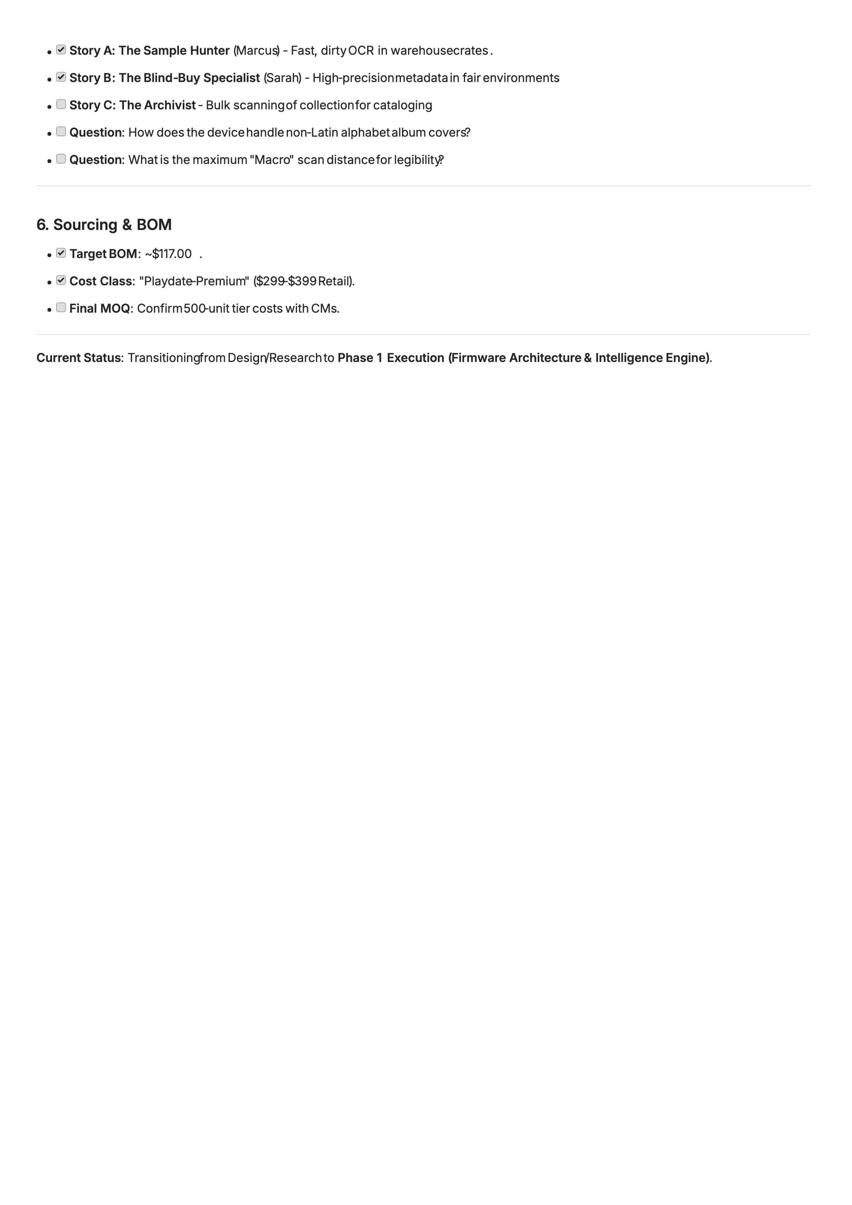
rendered_pages/Crate Iq Master Roadmap_p2.png
