keeganmoody33/YADIGGG/rendered_pages/Crate Iq Quick Start_p2.png

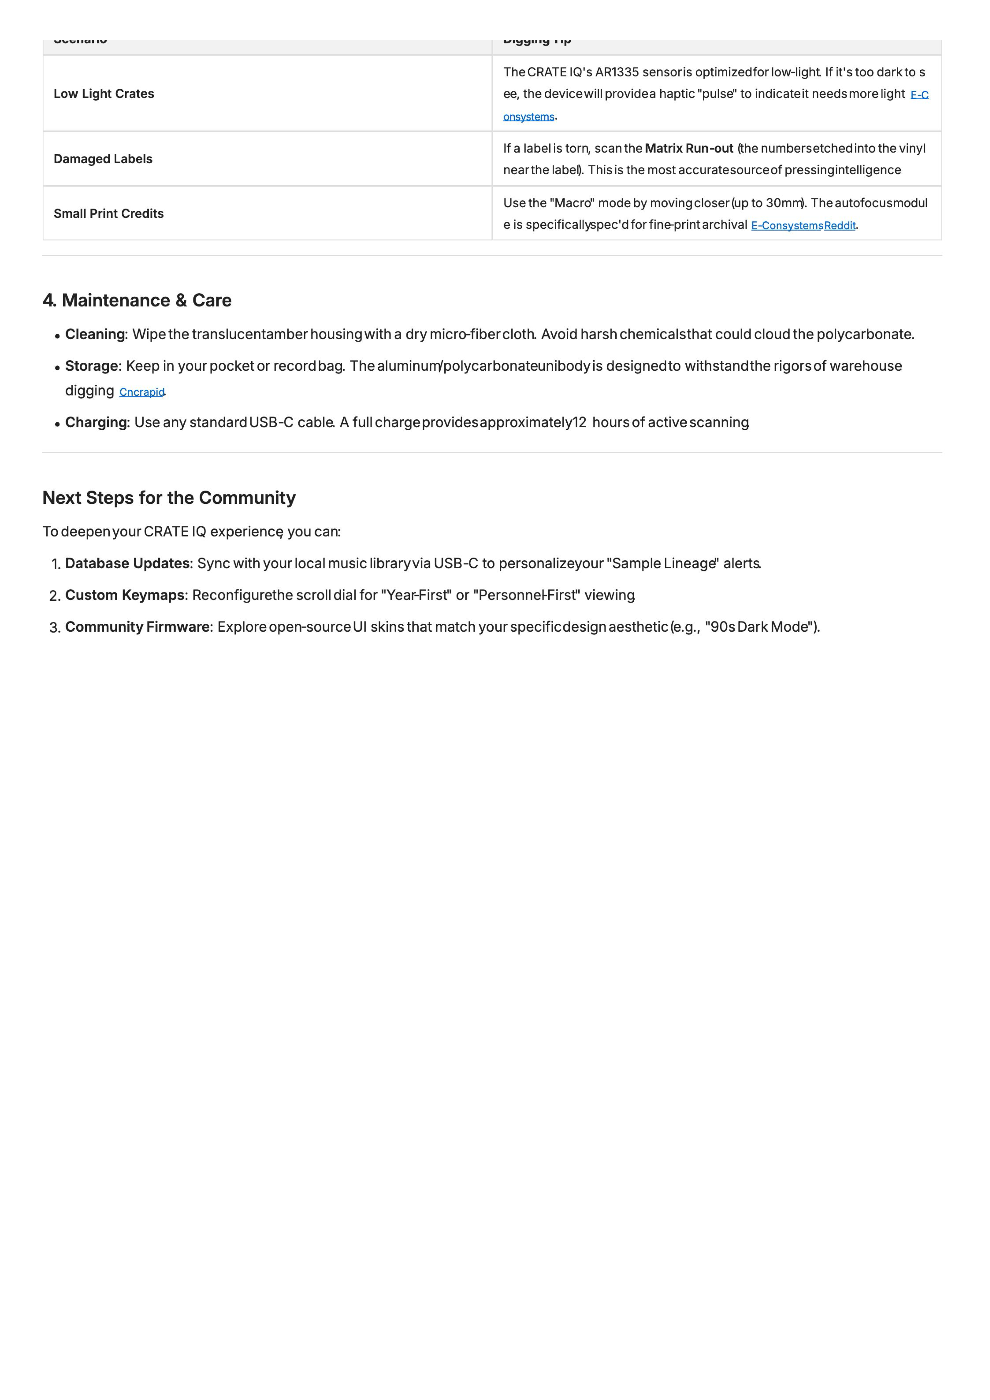
rendered_pages/Crate Iq Quick Start_p2.png
