keeganmoody33/YADIGGG/rendered_pages/Crate Iq Scope Document_p2.png

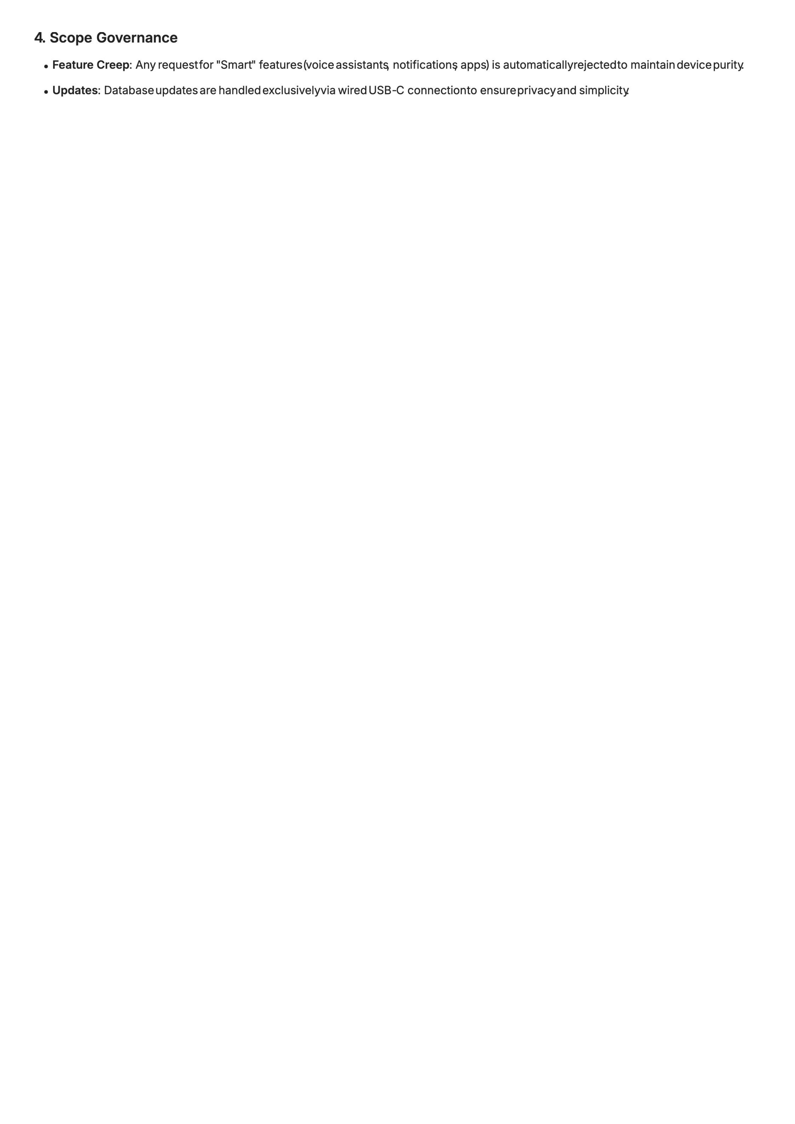
rendered_pages/Crate Iq Scope Document_p2.png
