keeganmoody33/YADIGGG/rendered_pages/Crate Iq Typography Final_p3.png

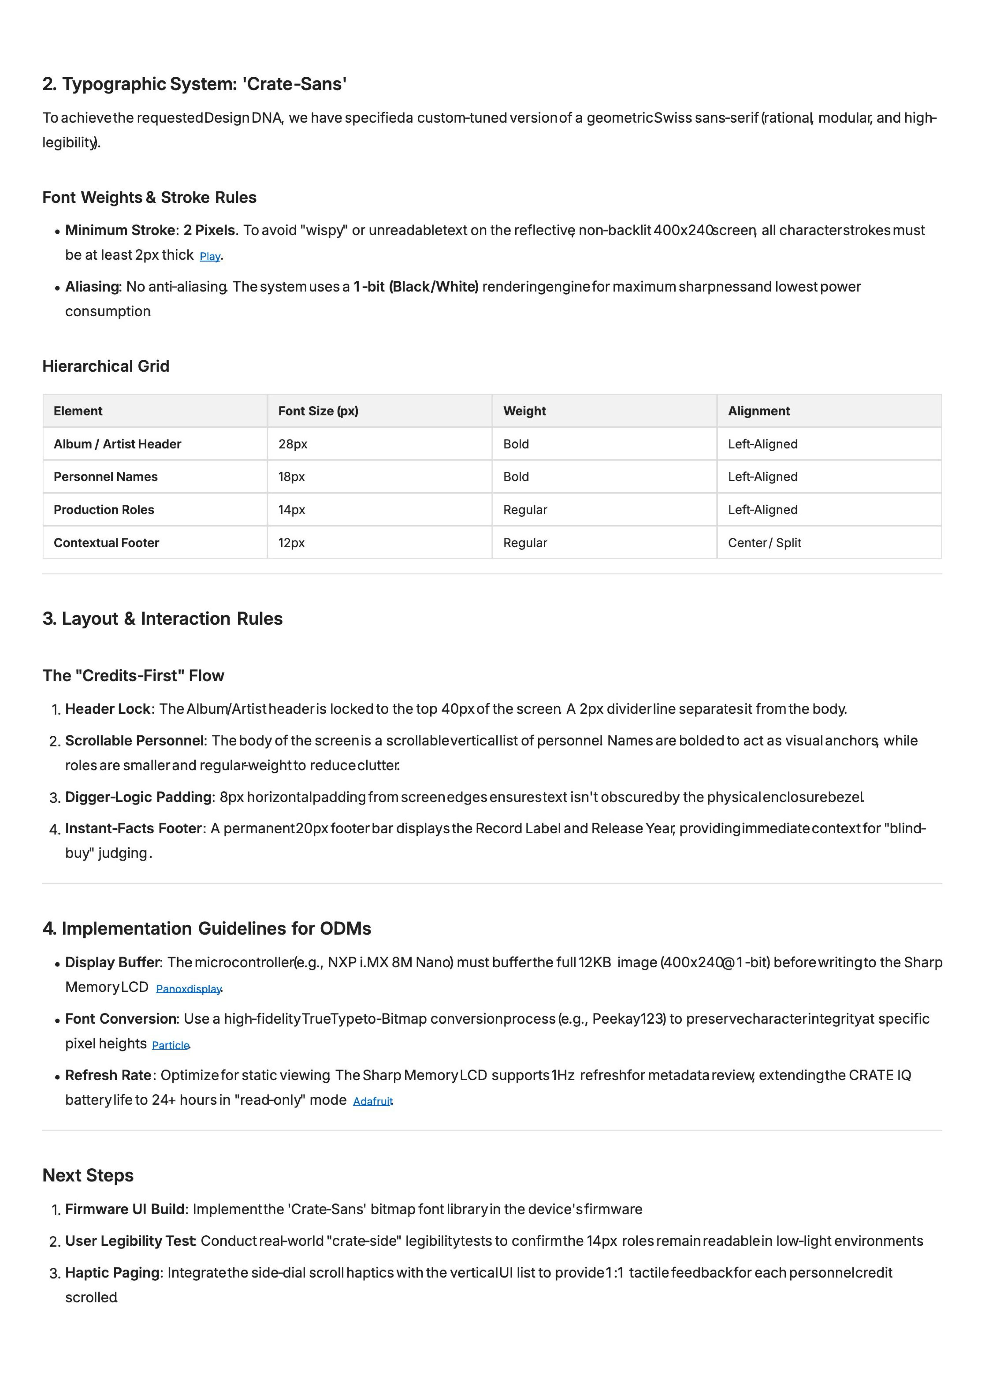
rendered_pages/Crate Iq Typography Final_p3.png
