keeganmoody33/YADIGGG/rendered_pages/Crate Iq User Interactions_p2.png

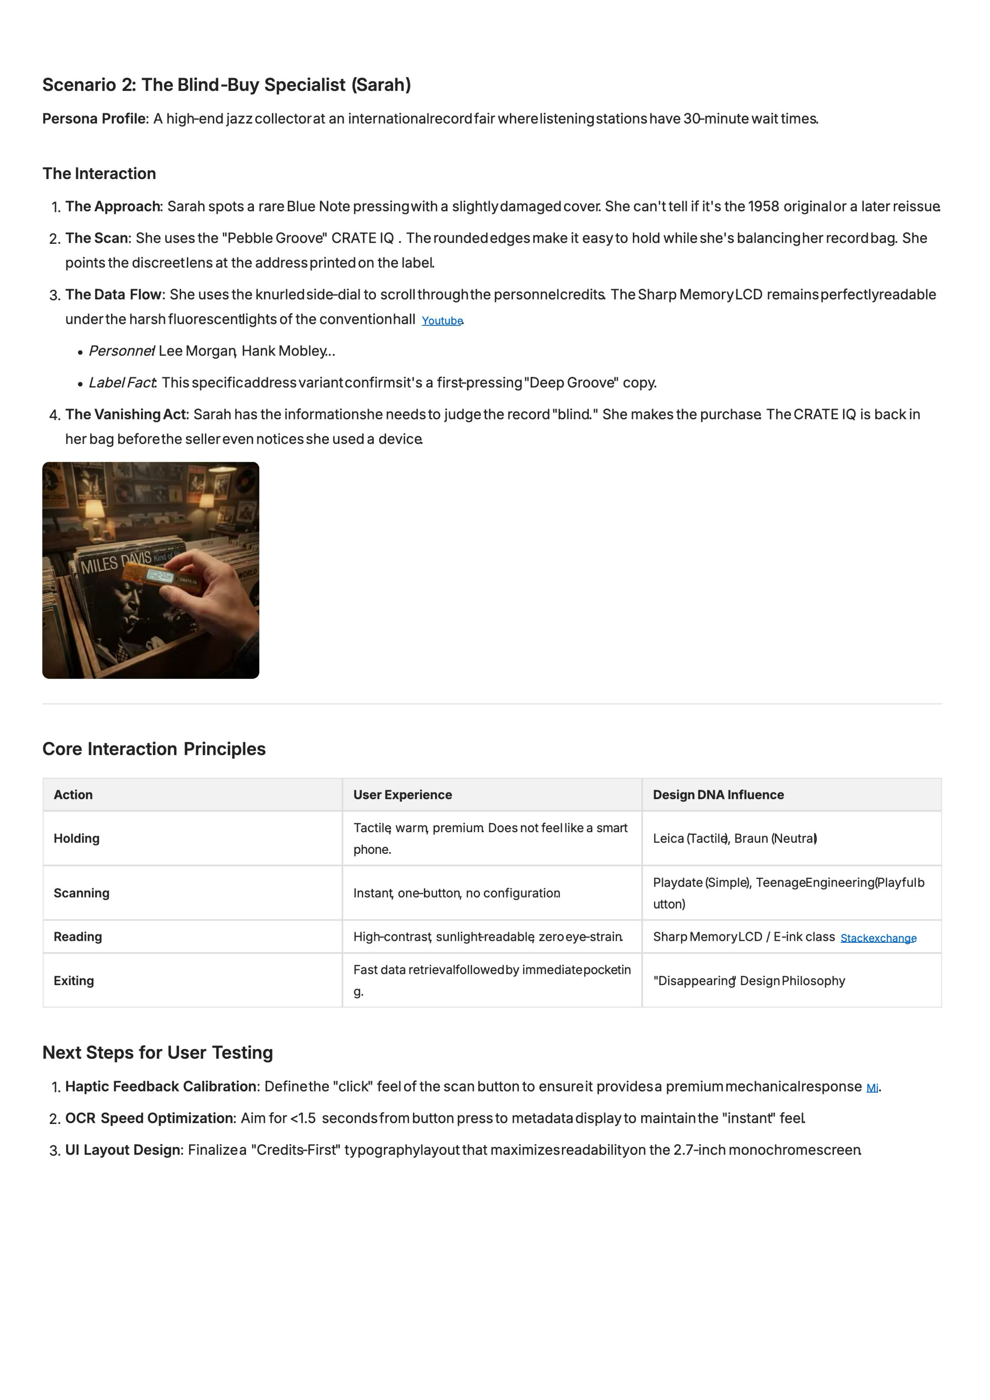
rendered_pages/Crate Iq User Interactions_p2.png
