keeganmoody33/YADIGGG/rendered_pages/Ya Diggg Official Tech Pack_p3.png

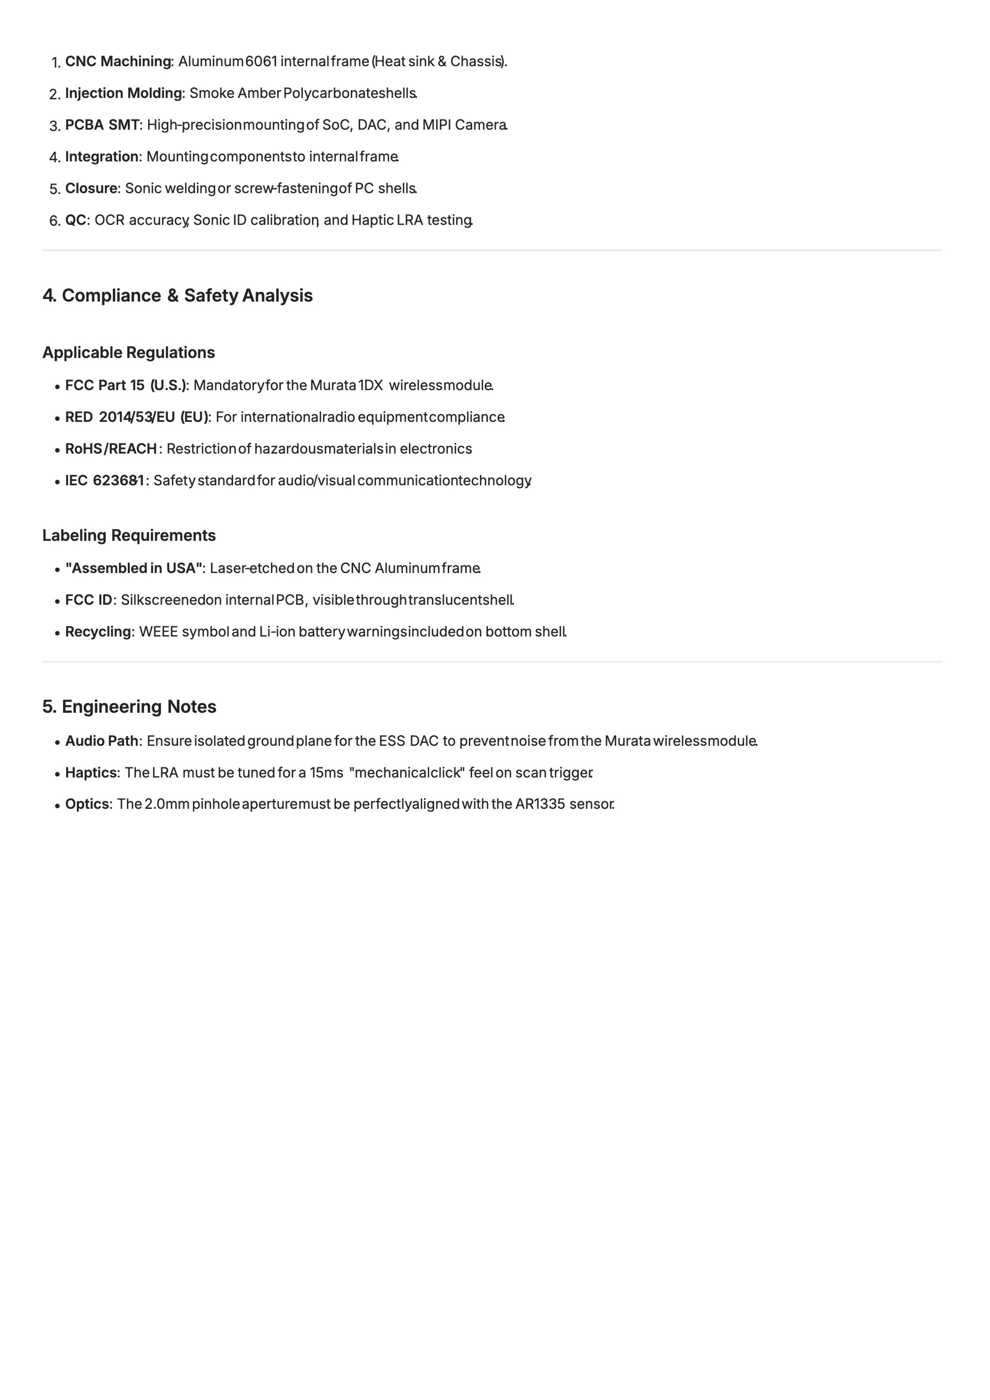
rendered_pages/Ya Diggg Official Tech Pack_p3.png
