keeganmoody33/YADIGGG/yadiggg_pinmux_routing.png

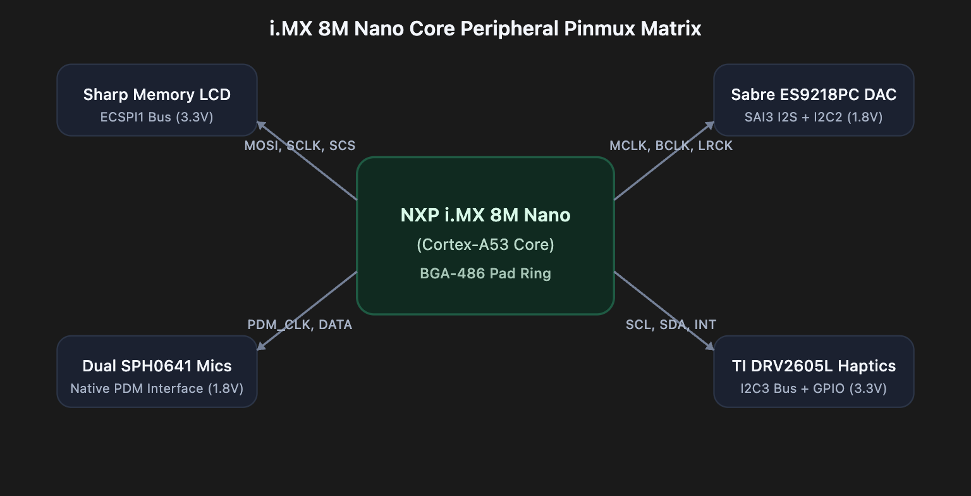
yadiggg_pinmux_routing.png
