keeganmoody33/YADIGGG/yadigggsketch_rendered.png

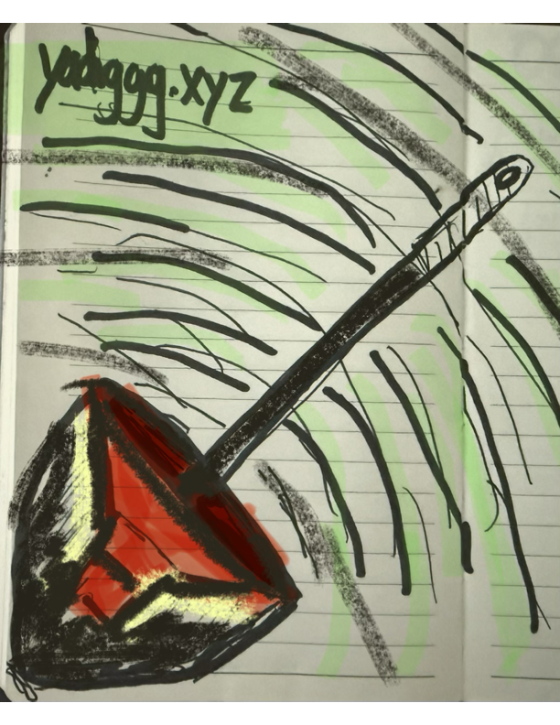
yadigggsketch_rendered.png
