keeganmoody33/YADIGGG/rendered_pages/Crate Iq Final Bom_p1.png

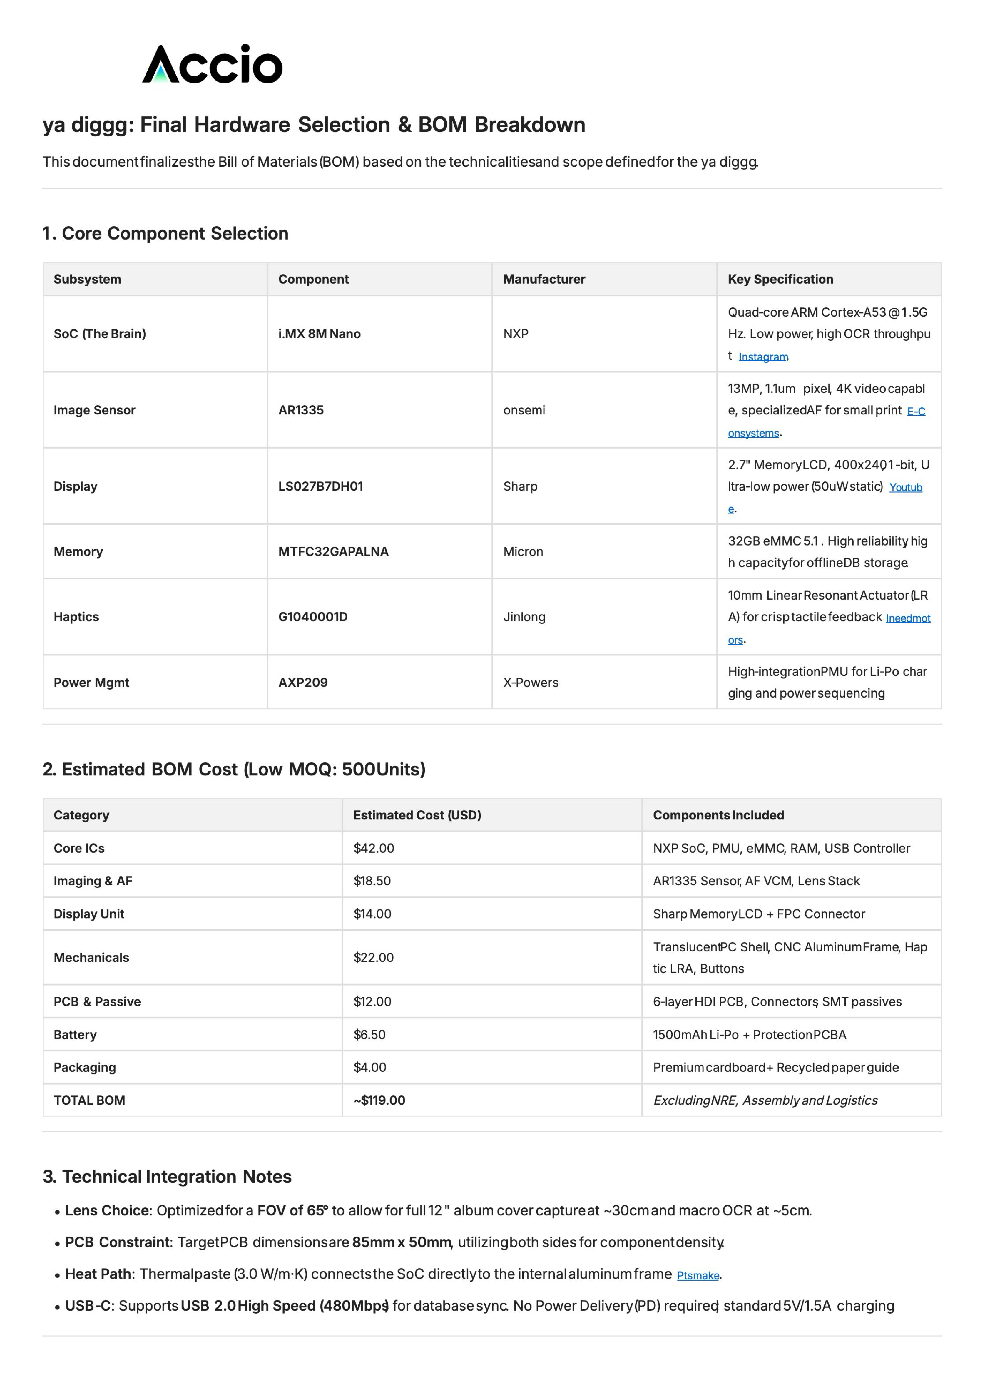
rendered_pages/Crate Iq Final Bom_p1.png
