keeganmoody33/YADIGGG/rendered_pages/Crate Iq Usa Sourcing Plan_p1.png

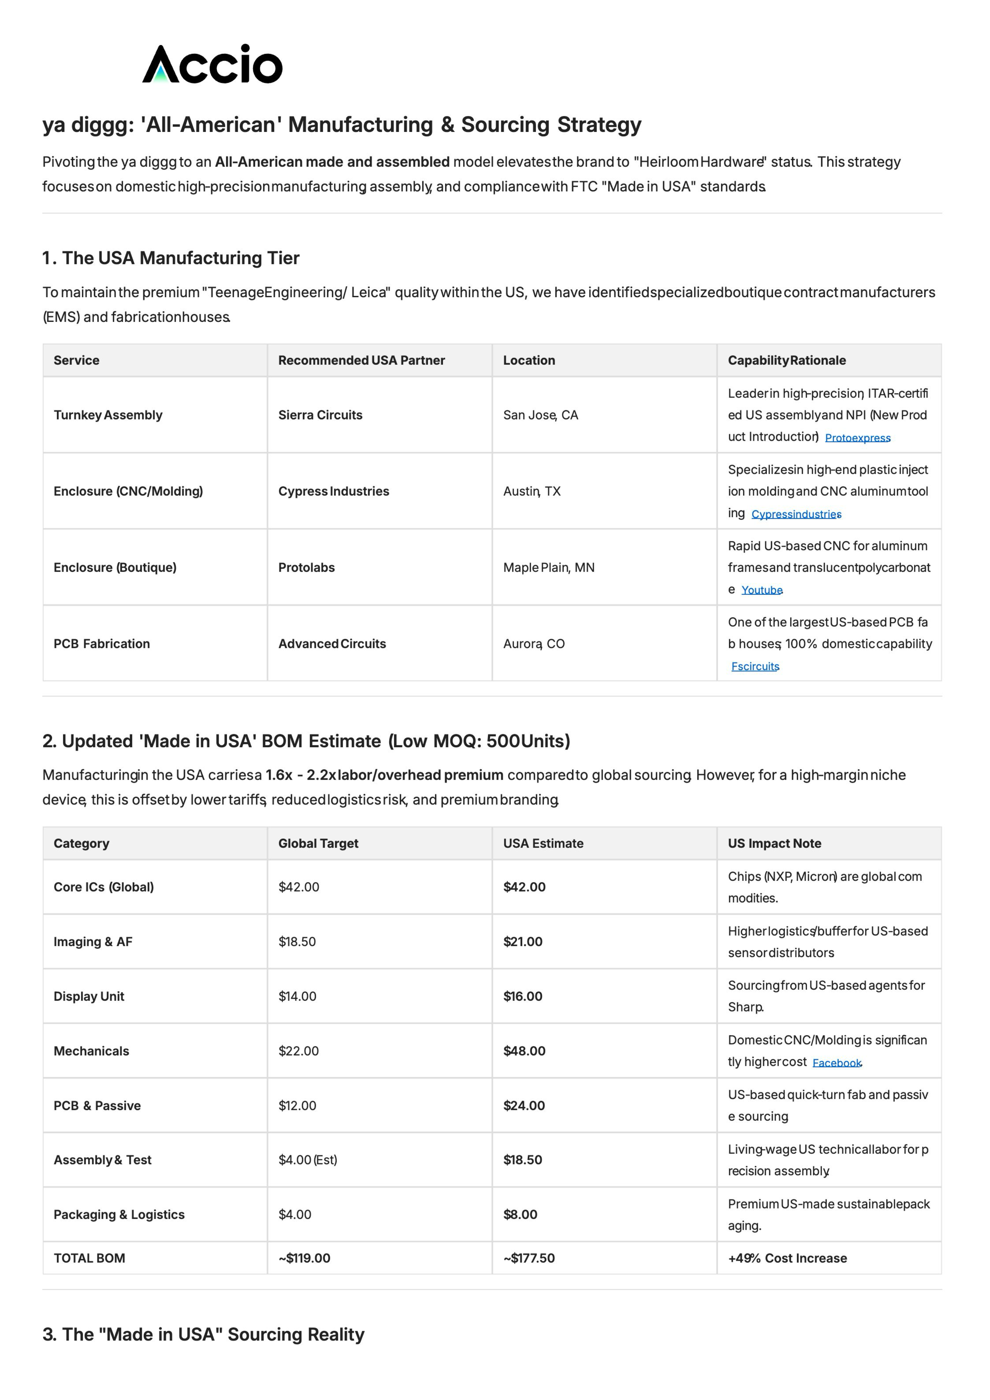
rendered_pages/Crate Iq Usa Sourcing Plan_p1.png
