keeganmoody33/YADIGGG/rendered_pages/Intelligence Engine Test_p1.png

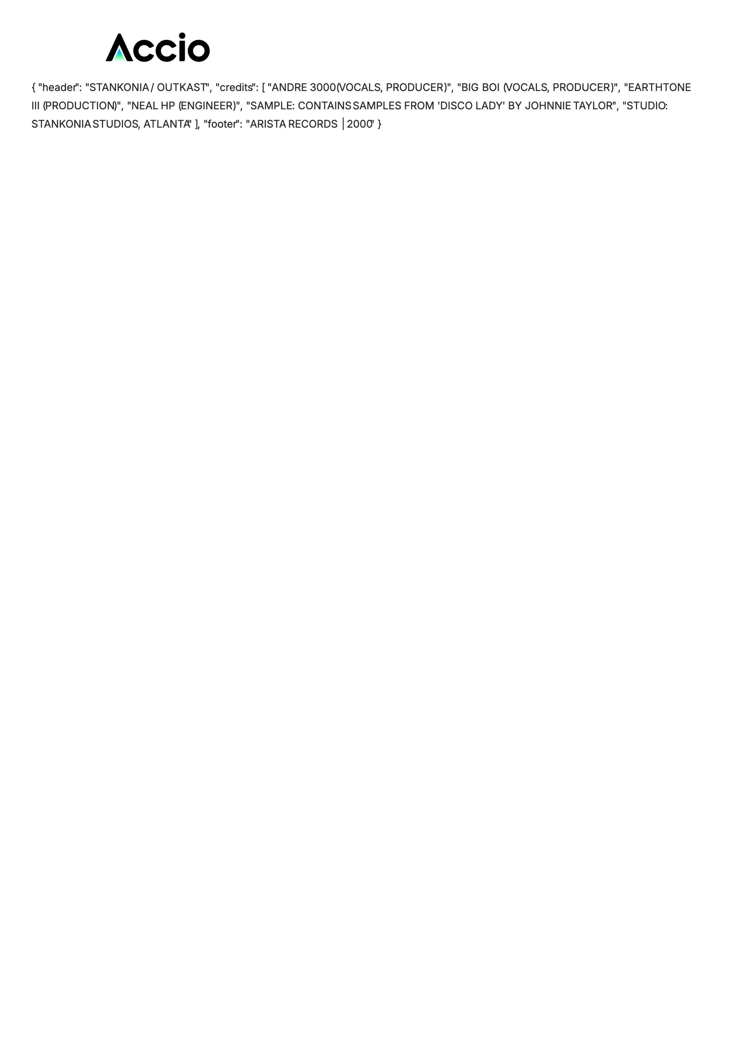
rendered_pages/Intelligence Engine Test_p1.png
